rick0x00/8bit-computer/HARDWARE/EDA/DOCUMENTS/ALU.png

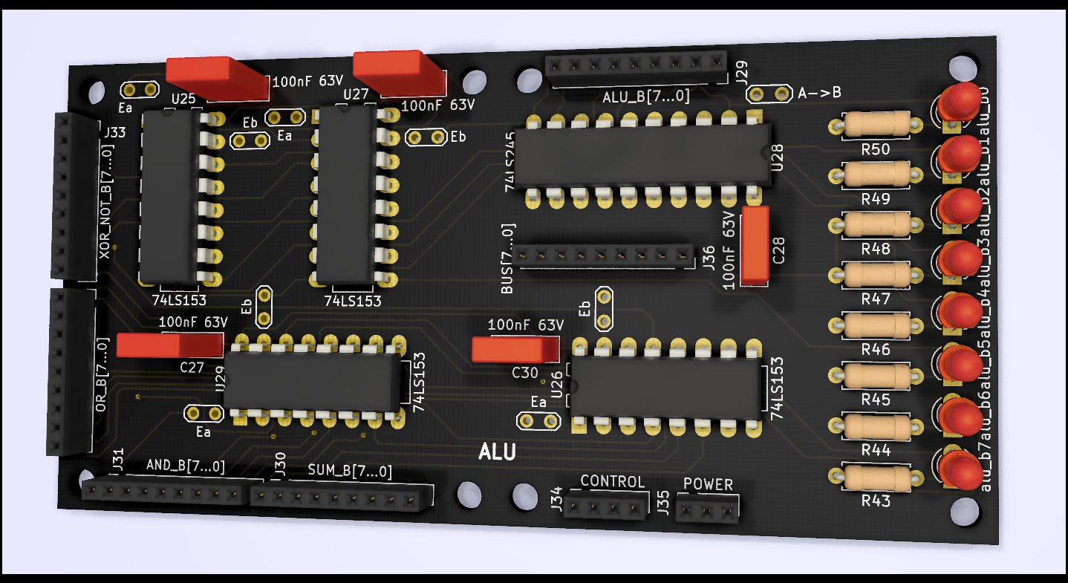
HARDWARE/EDA/DOCUMENTS/ALU.png
