rick0x00/8bit-computer/HARDWARE/EDA/DOCUMENTS/B Register.png

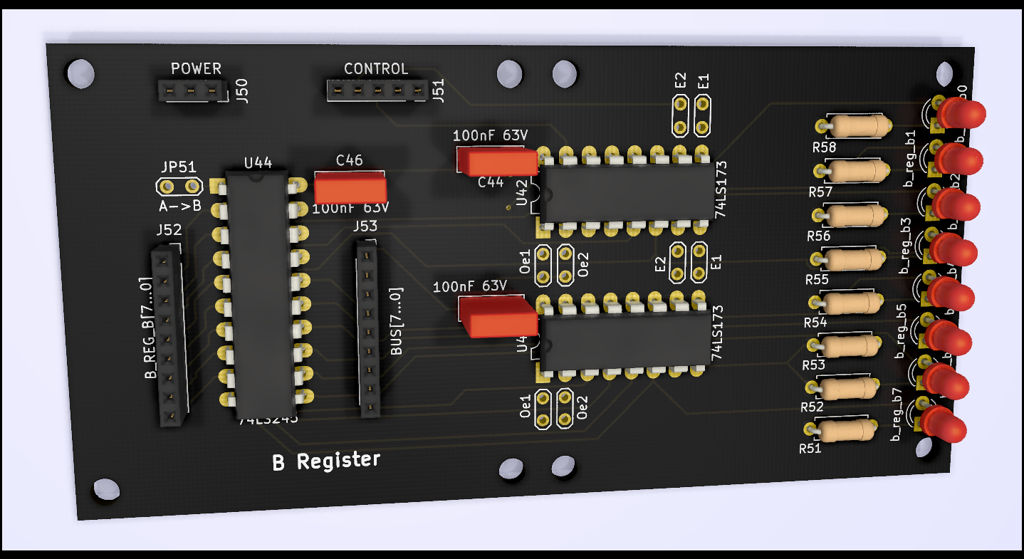
HARDWARE/EDA/DOCUMENTS/B Register.png
