rick0x00/8bit-computer/HARDWARE/EDA/DOCUMENTS/Bus Simulator.png

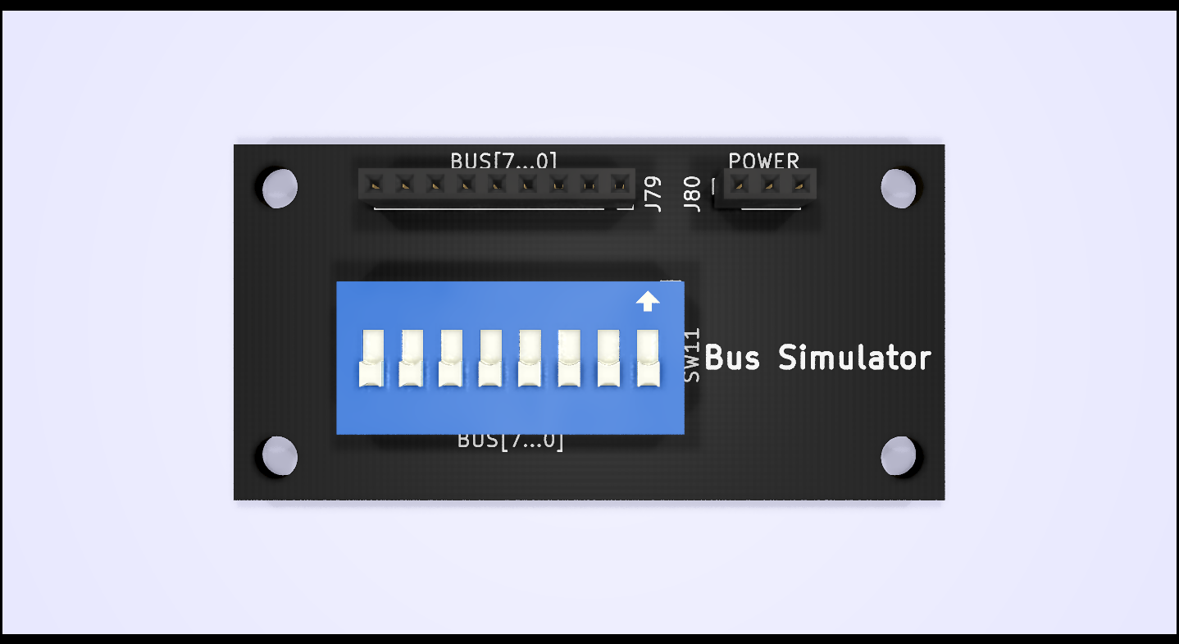
HARDWARE/EDA/DOCUMENTS/Bus Simulator.png
