rick0x00/8bit-computer/HARDWARE/EDA/DOCUMENTS/Clock Circuit.png

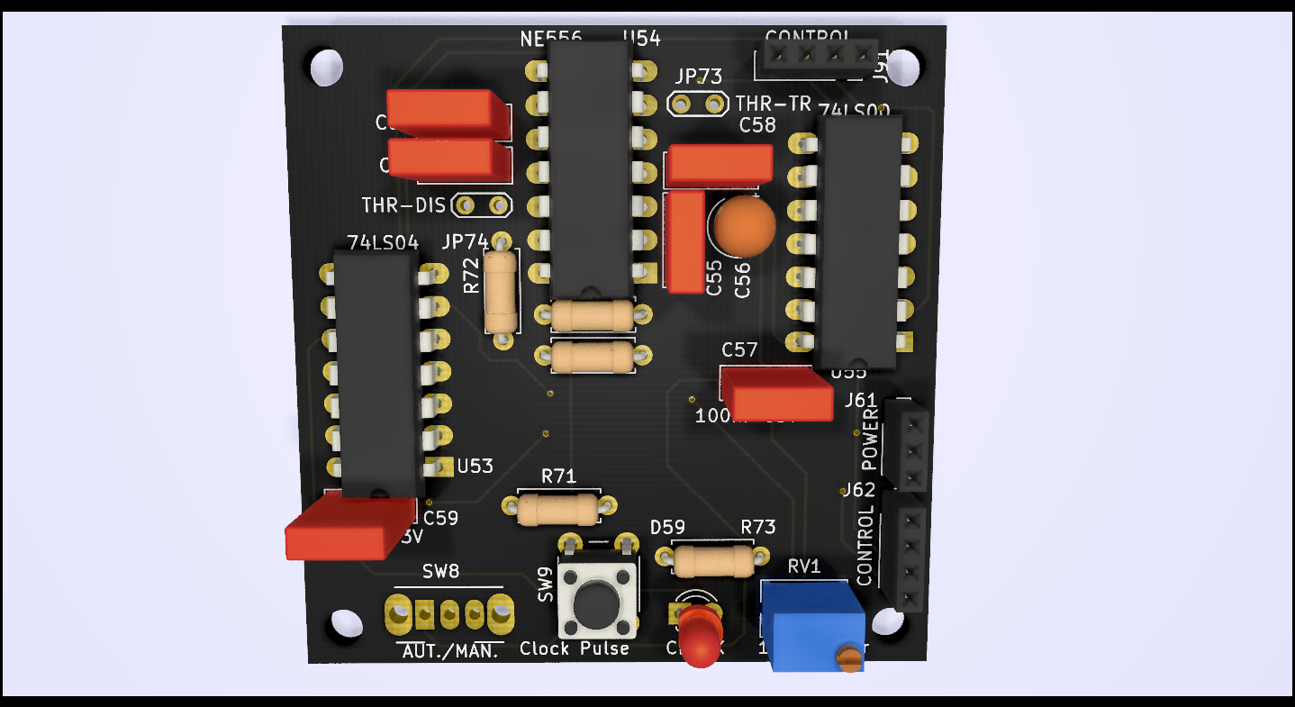
HARDWARE/EDA/DOCUMENTS/Clock Circuit.png
