rick0x00/8bit-computer/HARDWARE/EDA/DOCUMENTS/Control Decoder Simulator.png

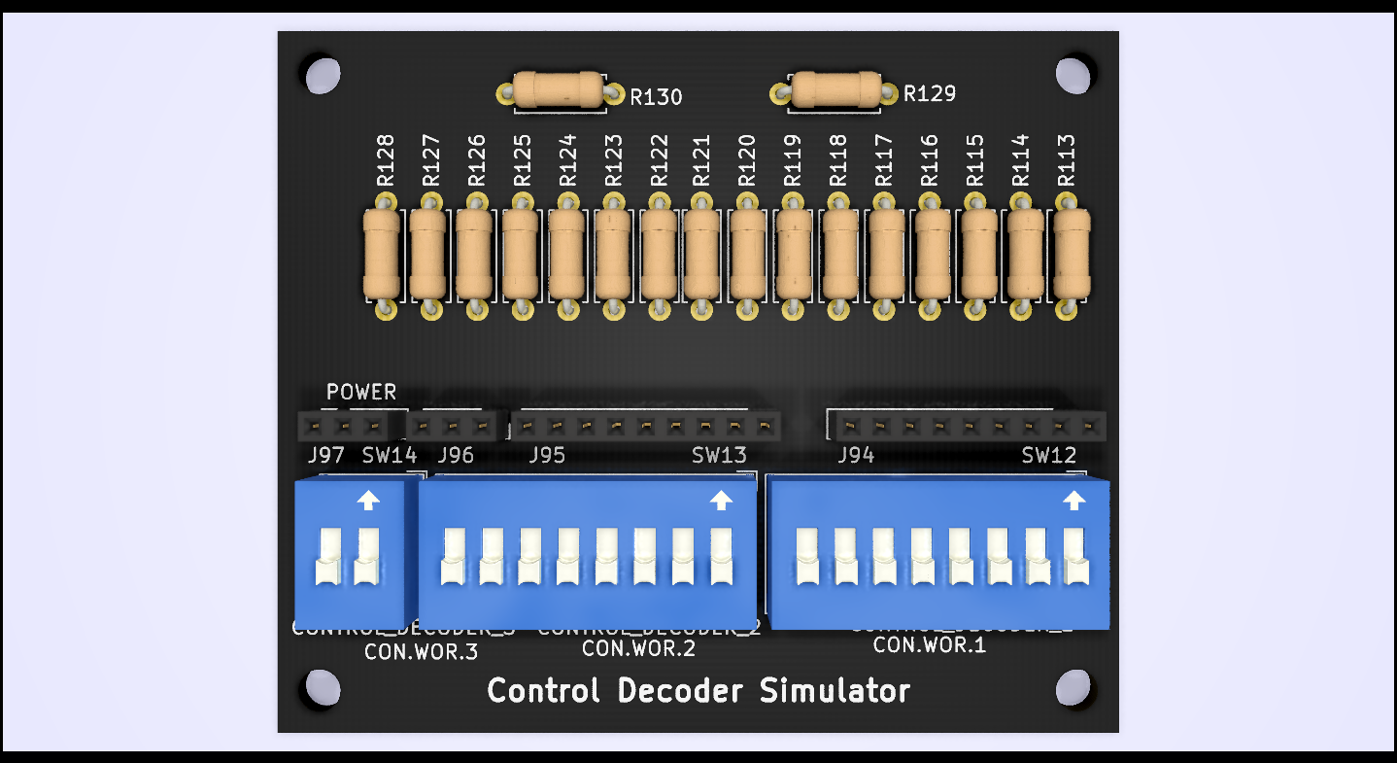
HARDWARE/EDA/DOCUMENTS/Control Decoder Simulator.png
