rick0x00/8bit-computer/HARDWARE/EDA/DOCUMENTS/Control Decoder.png

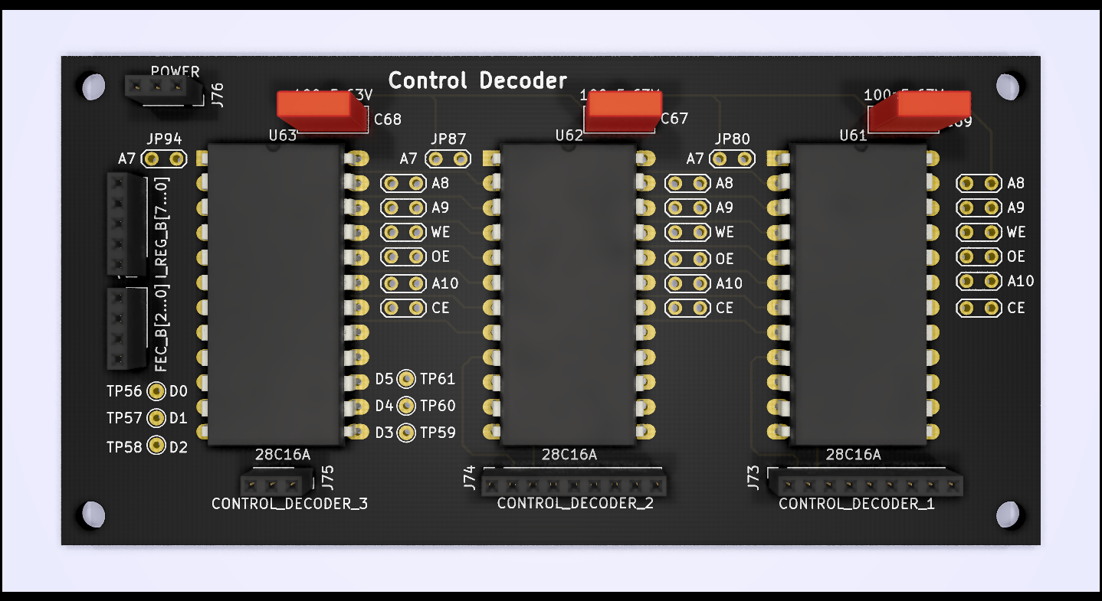
HARDWARE/EDA/DOCUMENTS/Control Decoder.png
