rick0x00/8bit-computer/HARDWARE/EDA/DOCUMENTS/Display.png

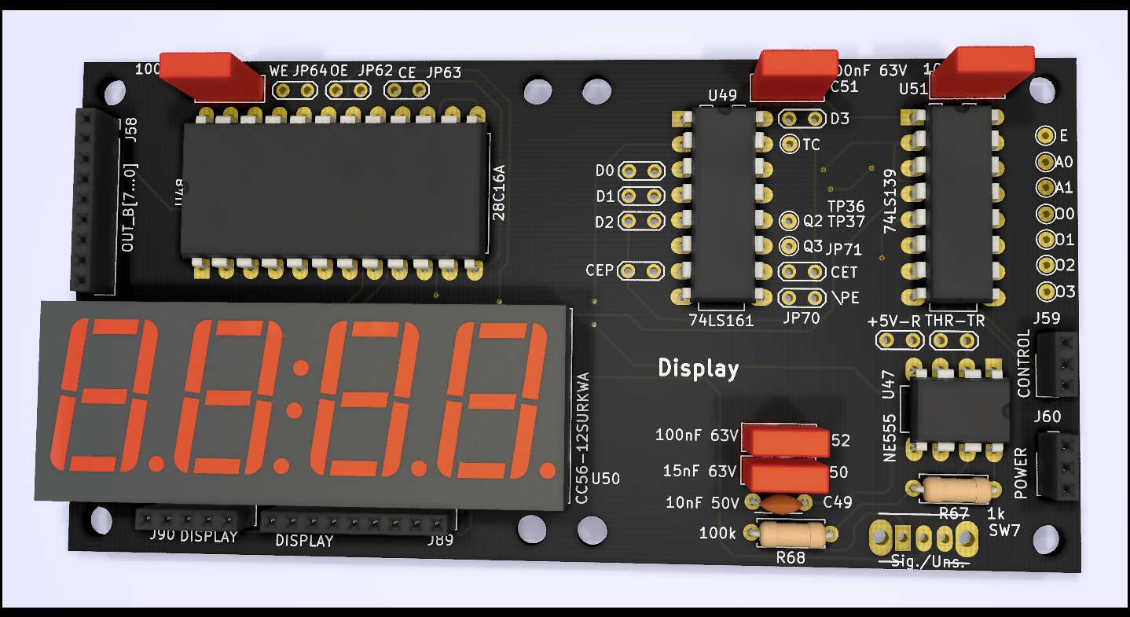
HARDWARE/EDA/DOCUMENTS/Display.png
