rick0x00/8bit-computer/HARDWARE/EDA/DOCUMENTS/hierarchy.png

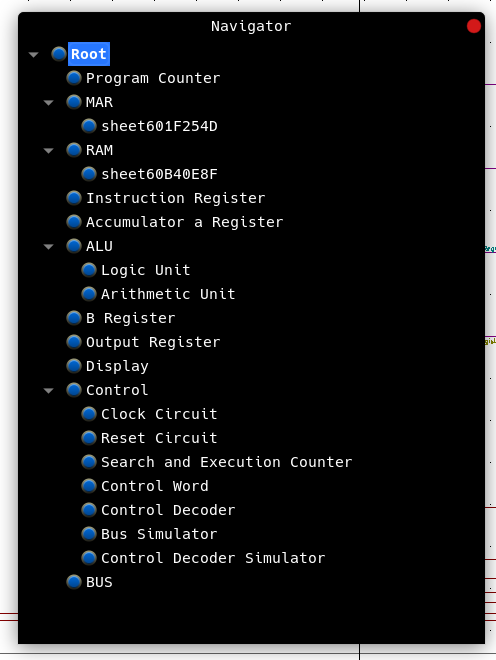
HARDWARE/EDA/DOCUMENTS/hierarchy.png
