rick0x00/8bit-computer/HARDWARE/EDA/DOCUMENTS/Logic Unit.png

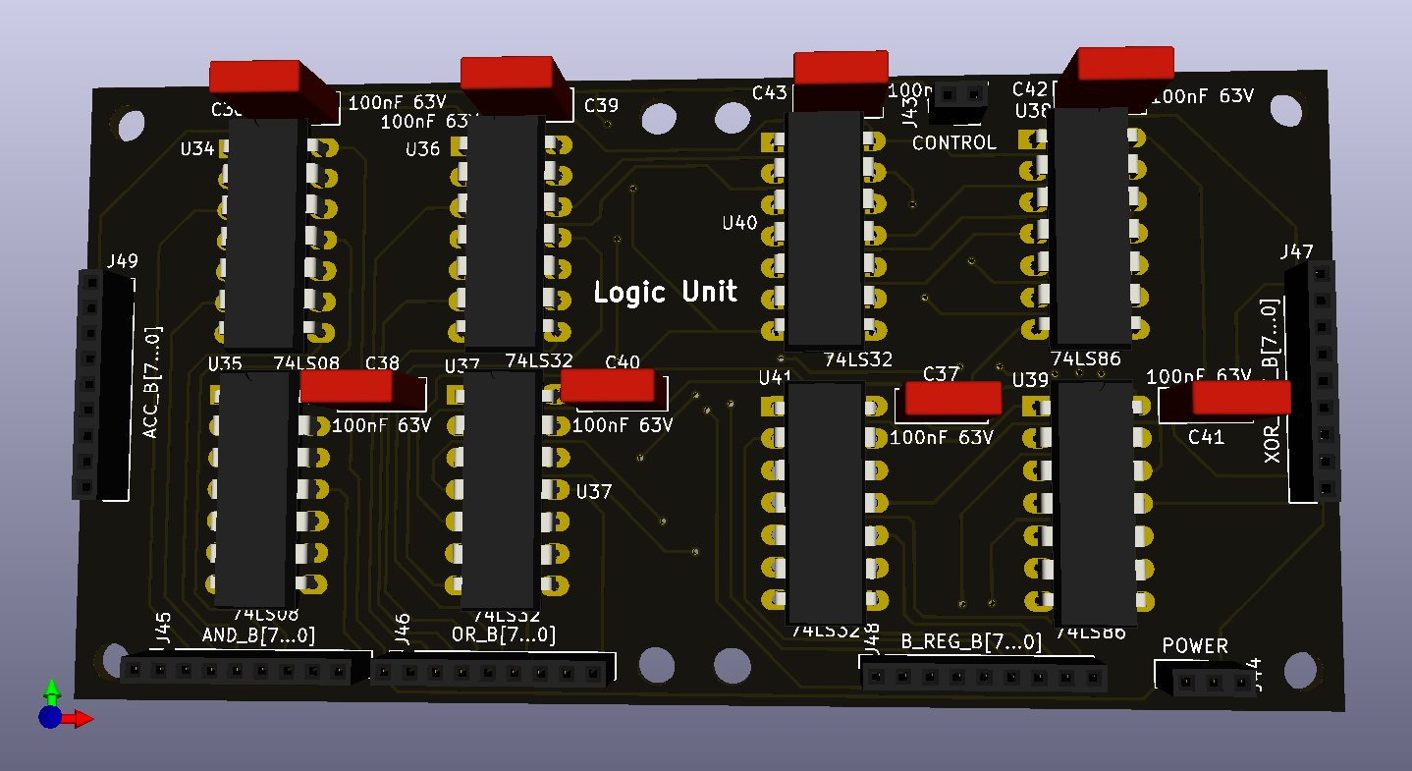
HARDWARE/EDA/DOCUMENTS/Logic Unit.png
