rick0x00/8bit-computer/HARDWARE/EDA/DOCUMENTS/Output Register.png

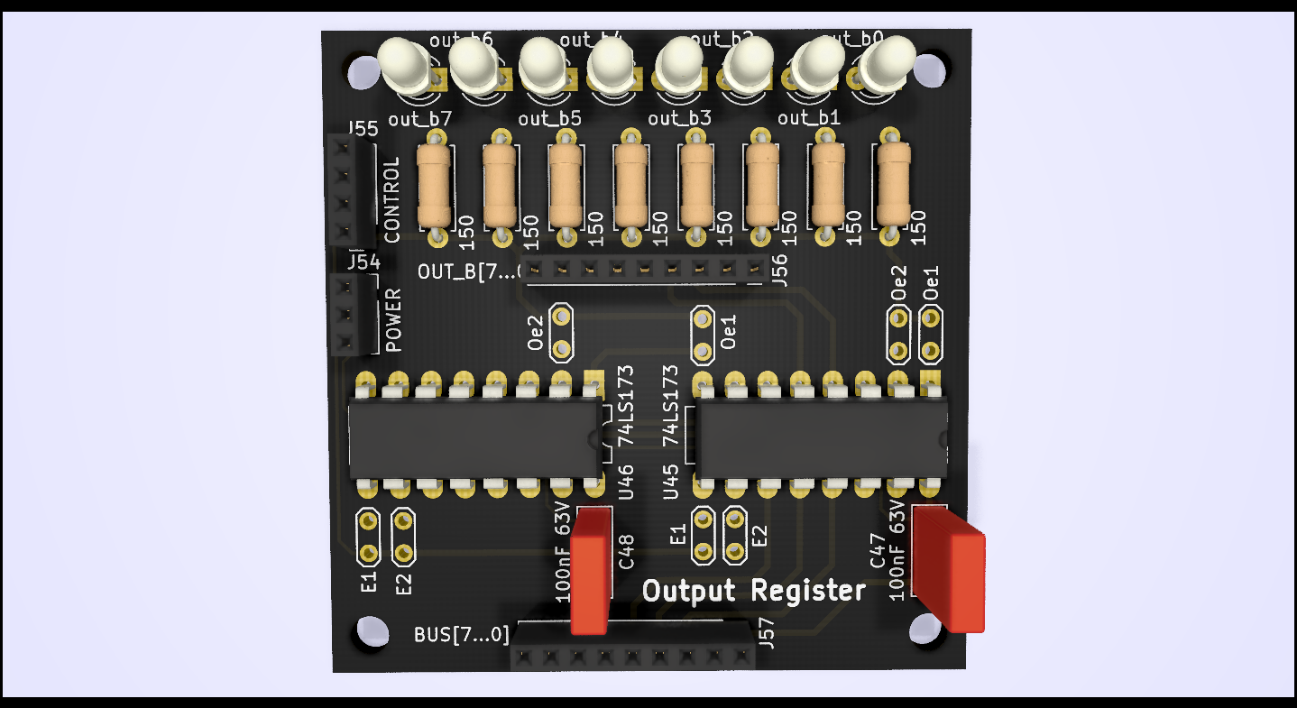
HARDWARE/EDA/DOCUMENTS/Output Register.png
