rick0x00/8bit-computer/HARDWARE/EDA/DOCUMENTS/Program Counter.png

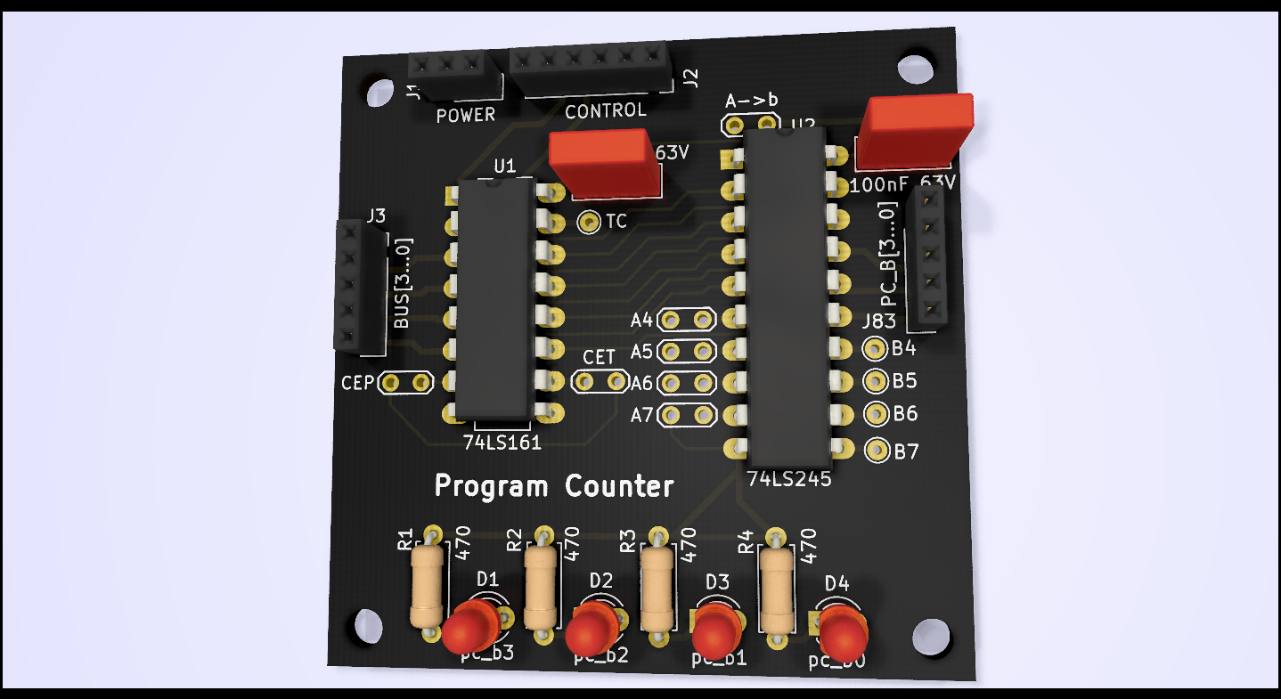
HARDWARE/EDA/DOCUMENTS/Program Counter.png
