rick0x00/8bit-computer/HARDWARE/EDA/DOCUMENTS/RAM.png

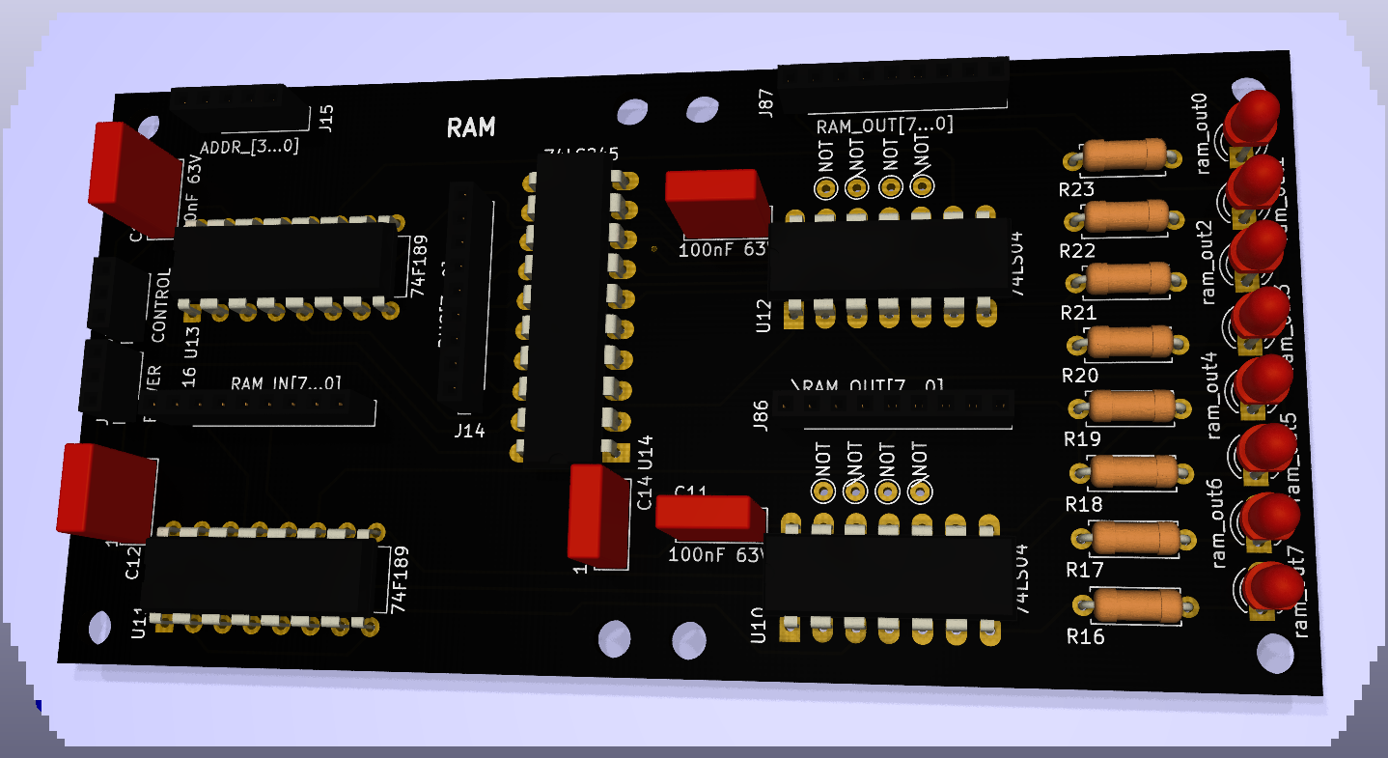
HARDWARE/EDA/DOCUMENTS/RAM.png
