rick0x00/8bit-computer/HARDWARE/EDA/DOCUMENTS/Search and Execution Counter.png

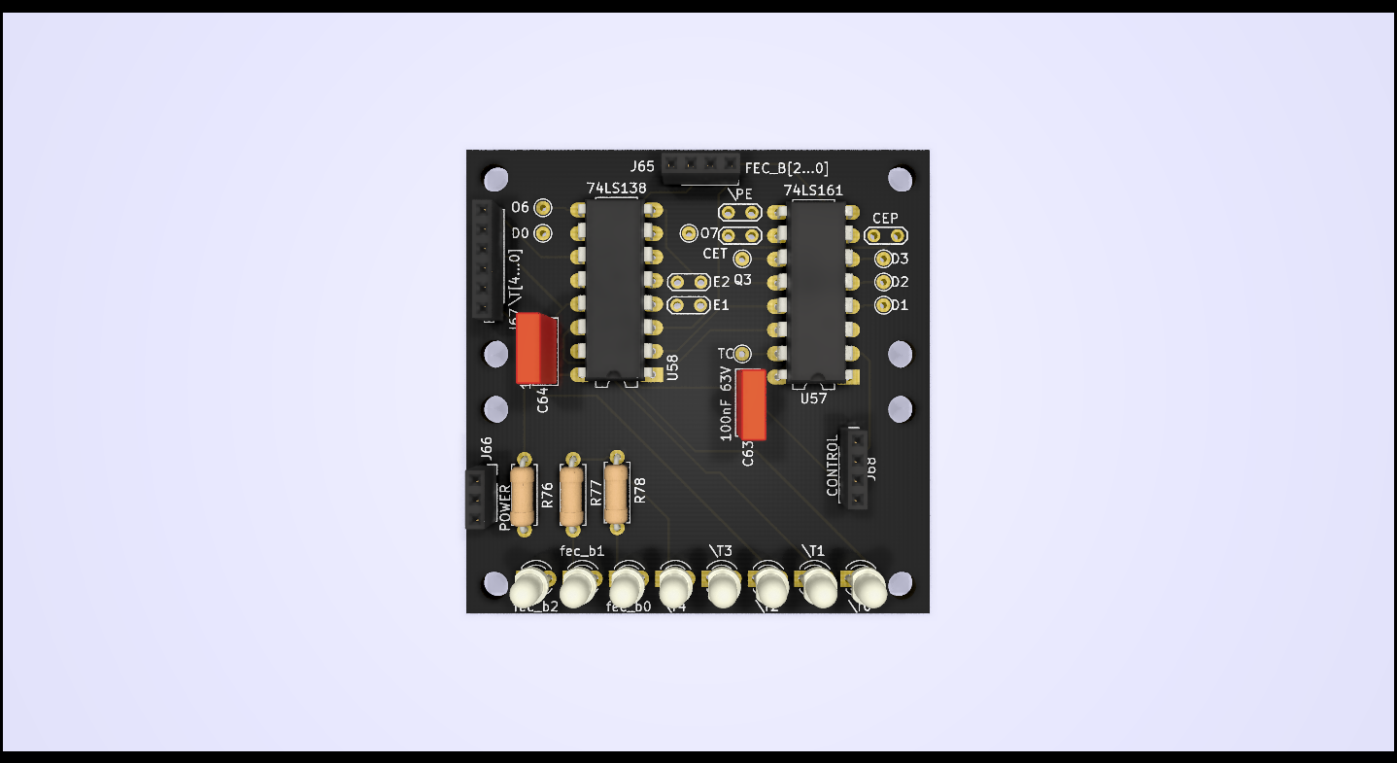
HARDWARE/EDA/DOCUMENTS/Search and Execution Counter.png
