rick0x00/8bit-computer/HARDWARE/EDA/DOCUMENTS/Selection Circuit.png

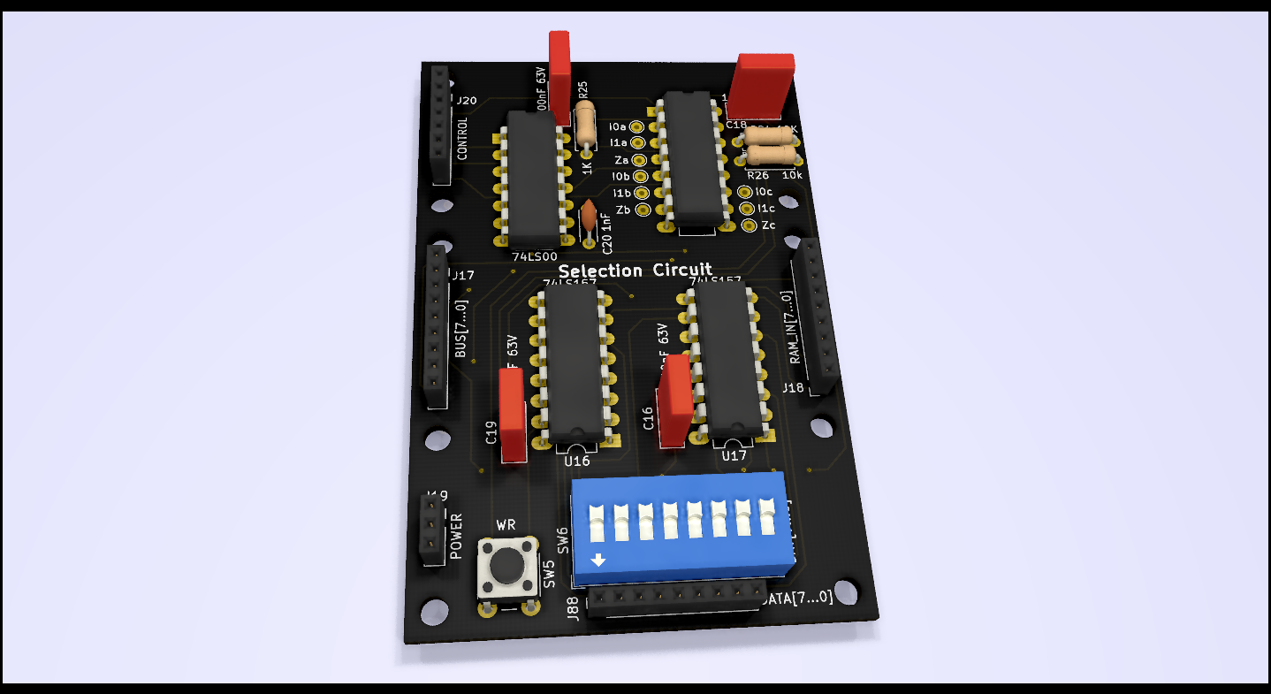
HARDWARE/EDA/DOCUMENTS/Selection Circuit.png
