rick0x00/8bit-computer/HARDWARE/EDA/DOCUMENTS/Instruction Register.png

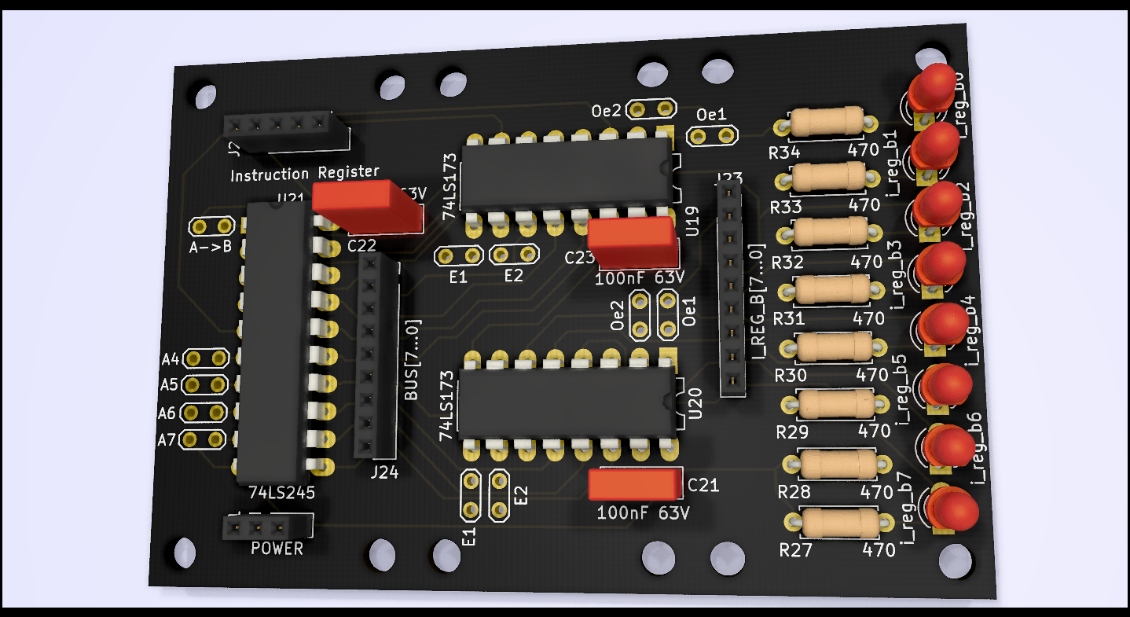
HARDWARE/EDA/DOCUMENTS/Instruction Register.png
