rick0x00/8bit-computer/HARDWARE/EDA/DOCUMENTS/BUS PCB.pdf

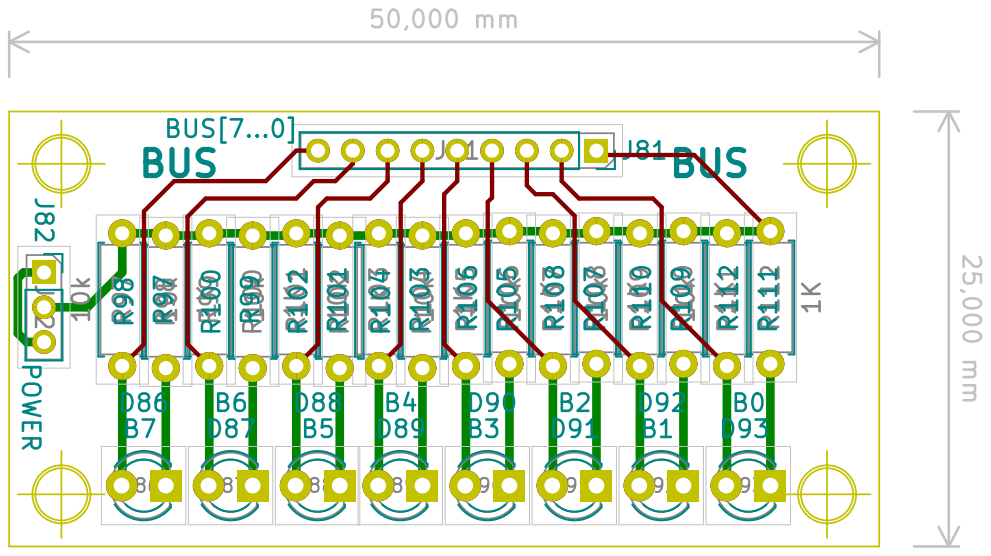
[picture p35: page 1]
