rick0x00/8bit-computer/HARDWARE/EDA/DOCUMENTS/Bus Simulator Black PCB.pdf

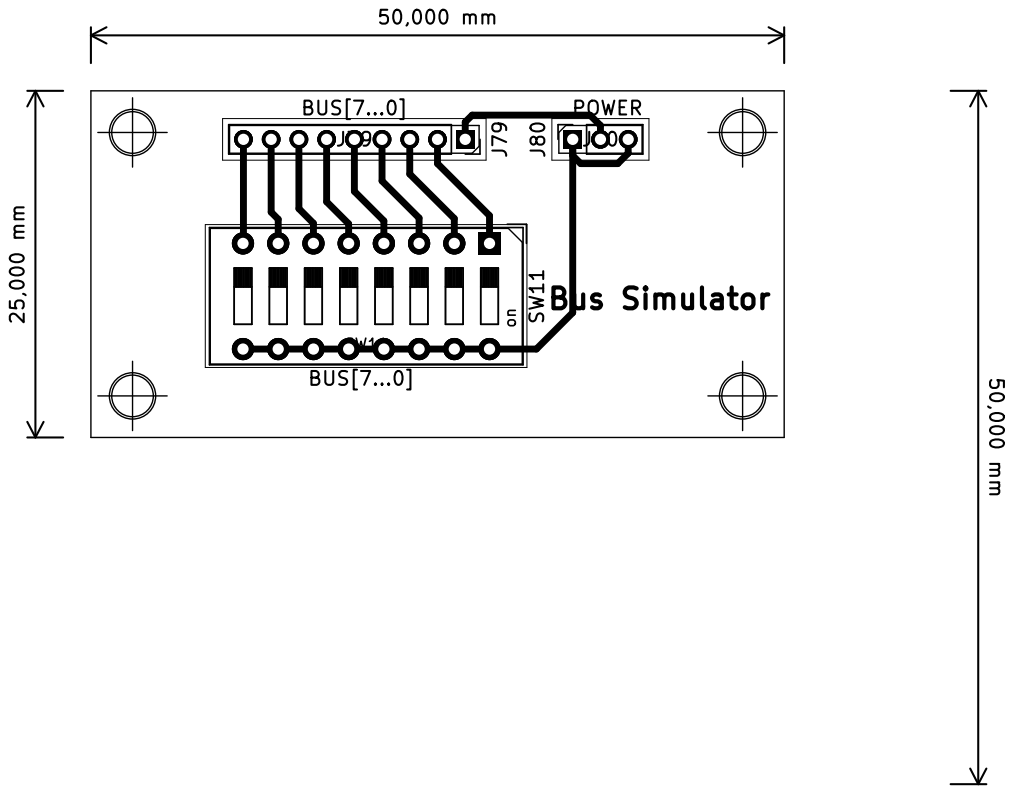
[picture p36: page 1]
