rick0x00/8bit-computer/HARDWARE/EDA/DOCUMENTS/Bus Simulator PCB.pdf

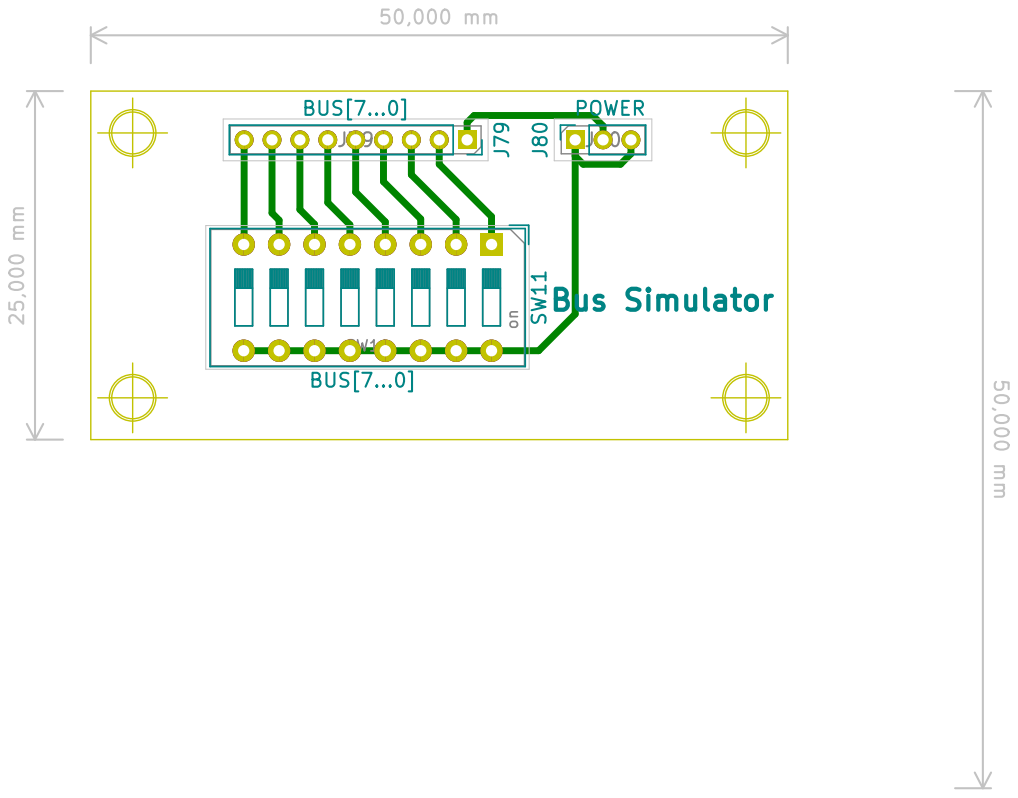
[picture p37: page 1]
