rick0x00/8bit-computer/HARDWARE/EDA/DOCUMENTS/Clock Circuit Black PCB.pdf

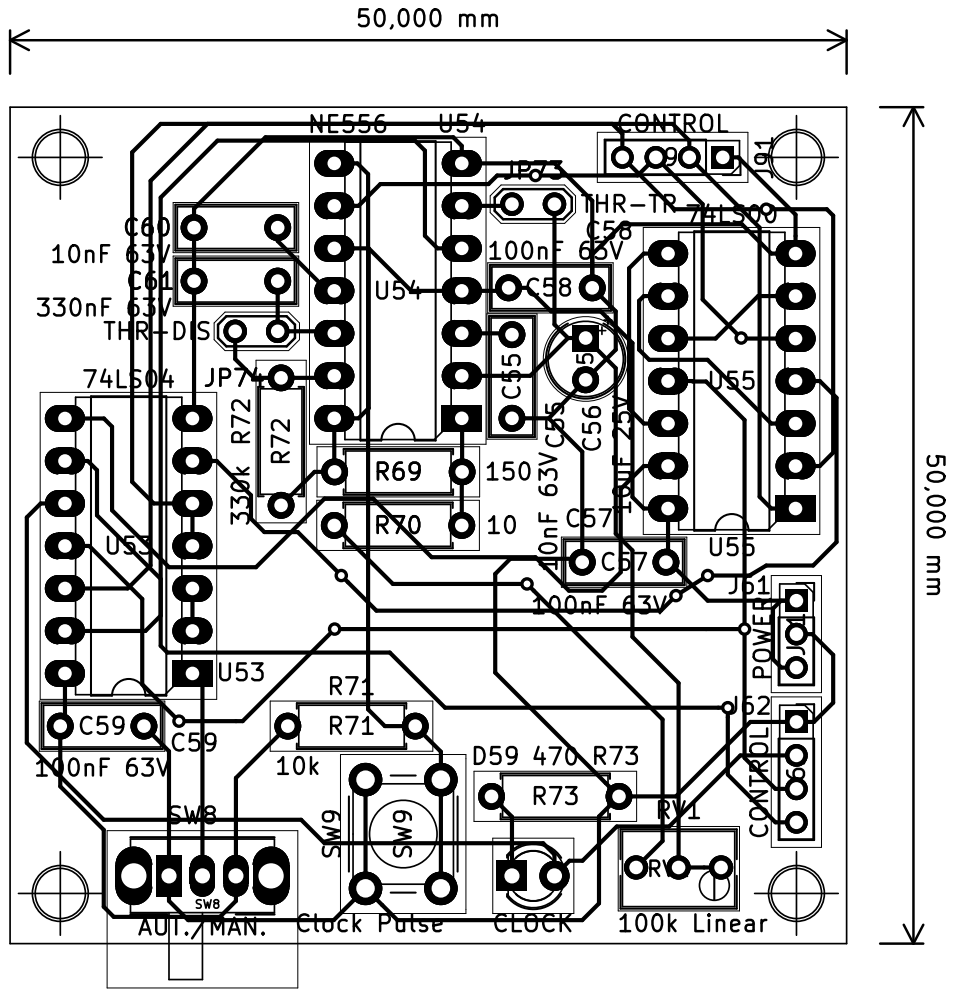
[picture p38: page 1]
