rick0x00/8bit-computer/HARDWARE/EDA/DOCUMENTS/Clock Circuit PCB.pdf

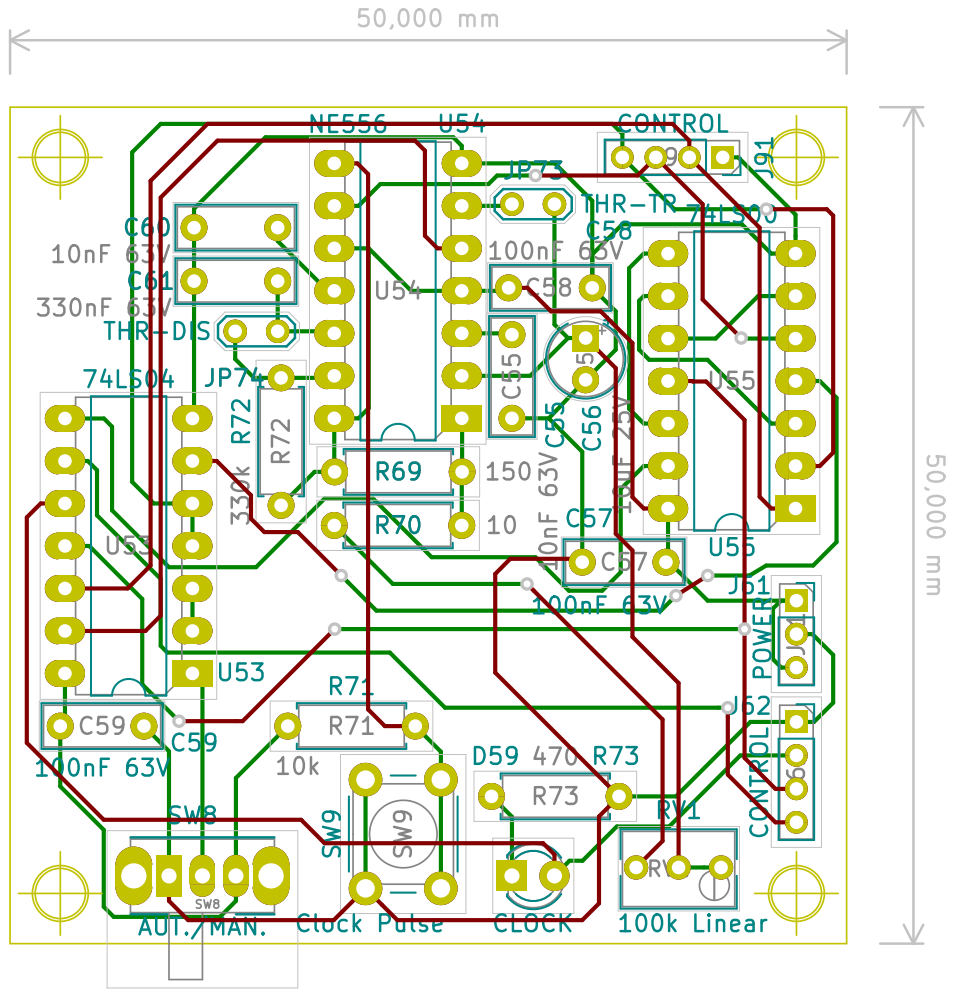
[picture p39: page 1]
