rick0x00/8bit-computer/HARDWARE/EDA/DOCUMENTS/Control Decoder Black PCB.pdf

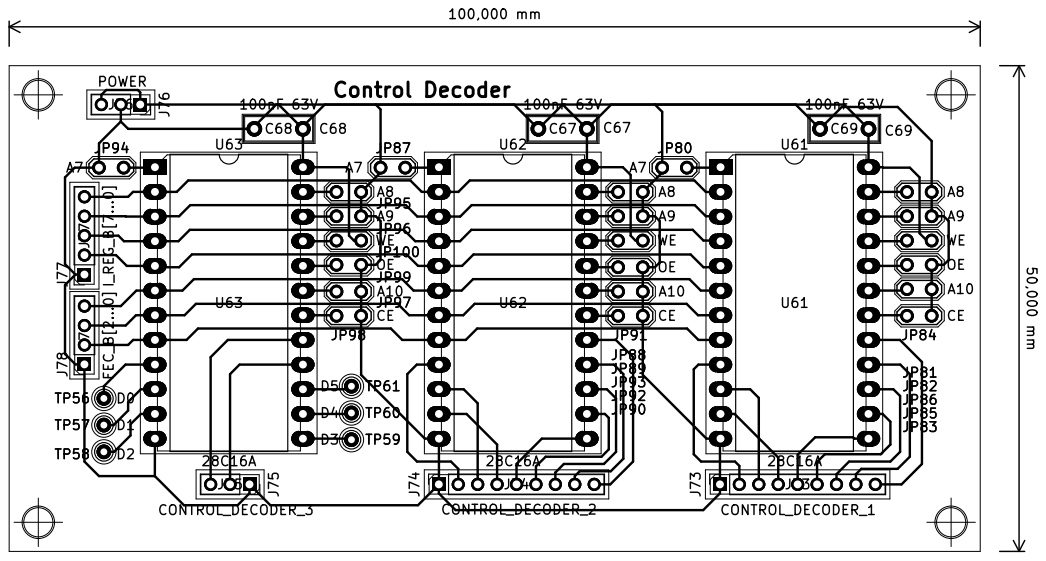
[picture p40: page 1]
