rick0x00/8bit-computer/HARDWARE/EDA/DOCUMENTS/Control Decoder PCB.pdf

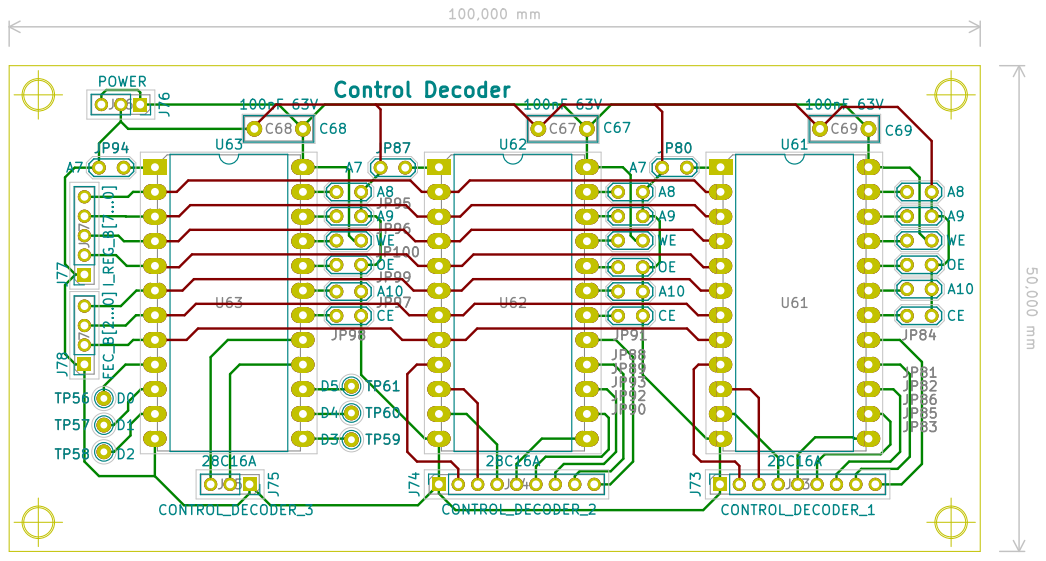
[picture p41: page 1]
