rick0x00/8bit-computer/HARDWARE/EDA/DOCUMENTS/Control Decoder Simulator Black PCB.pdf

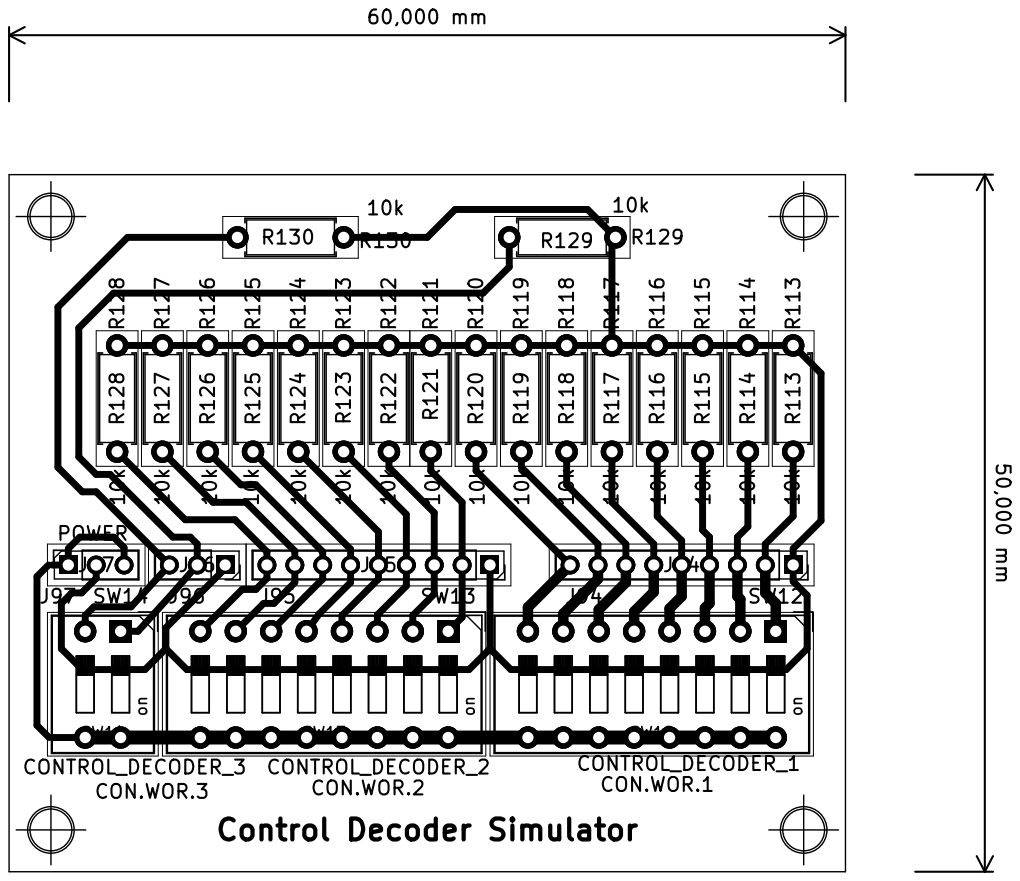
[picture p42: page 1]
