rick0x00/8bit-computer/HARDWARE/EDA/DOCUMENTS/Control Decoder Simulator PCB.pdf

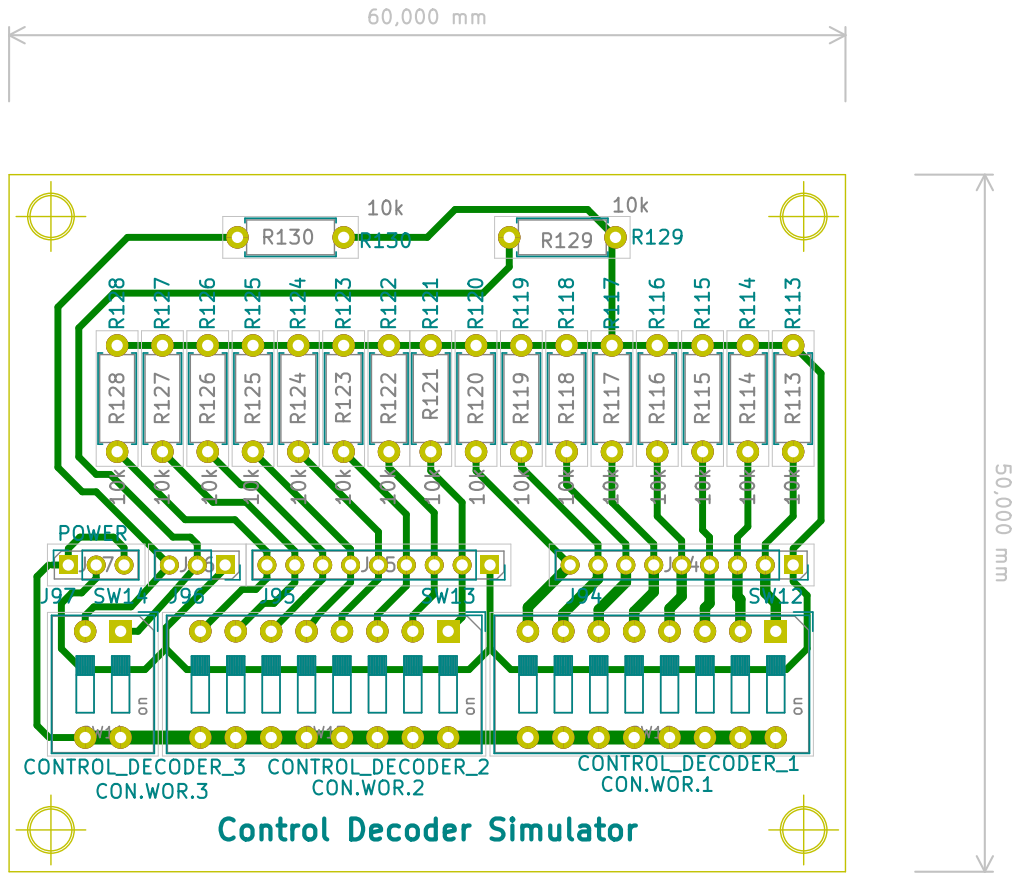
[picture p43: page 1]
