rick0x00/8bit-computer/HARDWARE/EDA/DOCUMENTS/Control Word Black PCB.pdf

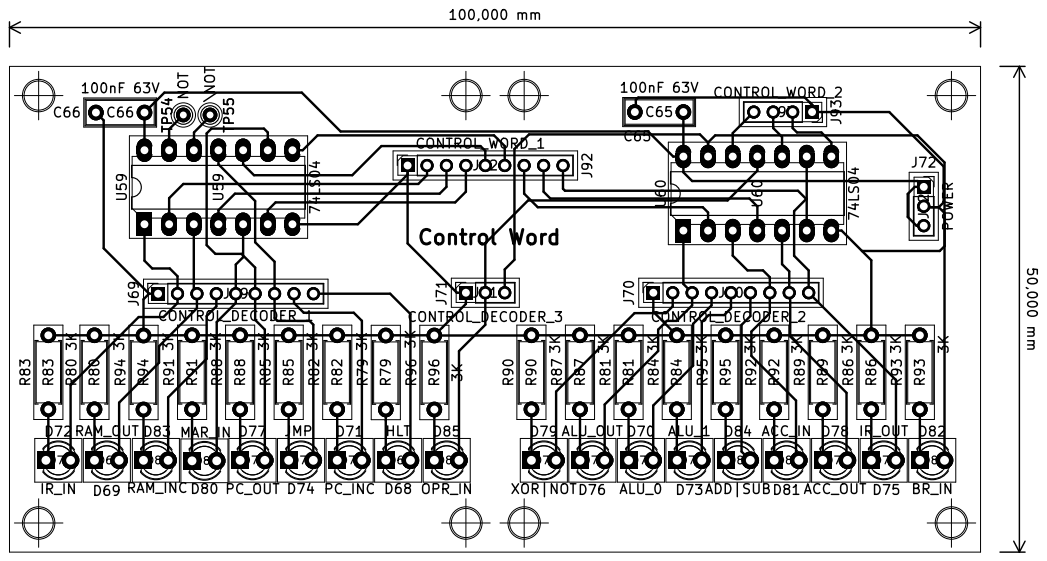
[picture p44: page 1]
