rick0x00/8bit-computer/HARDWARE/EDA/DOCUMENTS/Control Word PCB.pdf

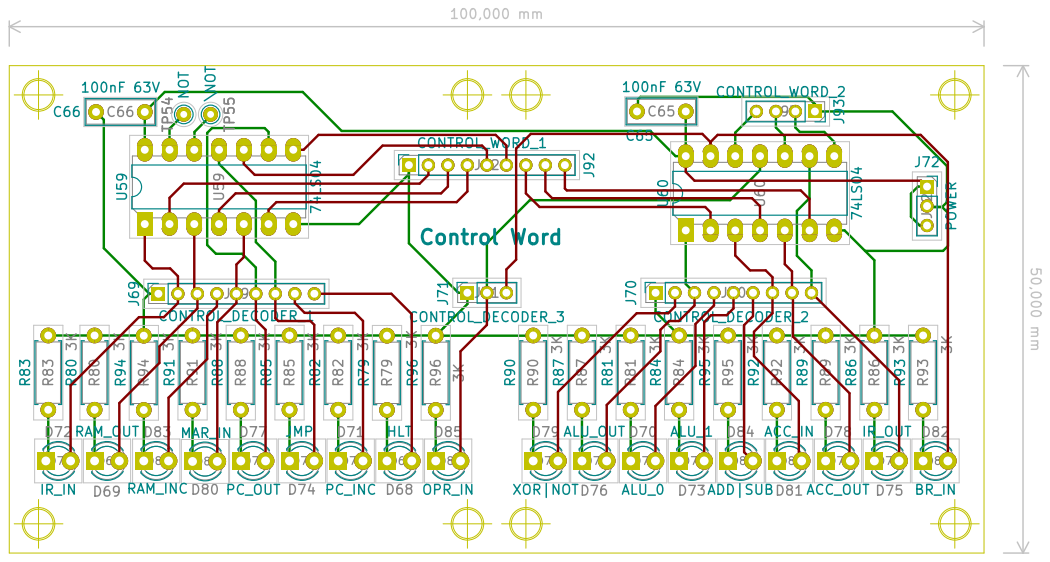
[picture p45: page 1]
