rick0x00/8bit-computer/HARDWARE/EDA/DOCUMENTS/Display Black PCB.pdf

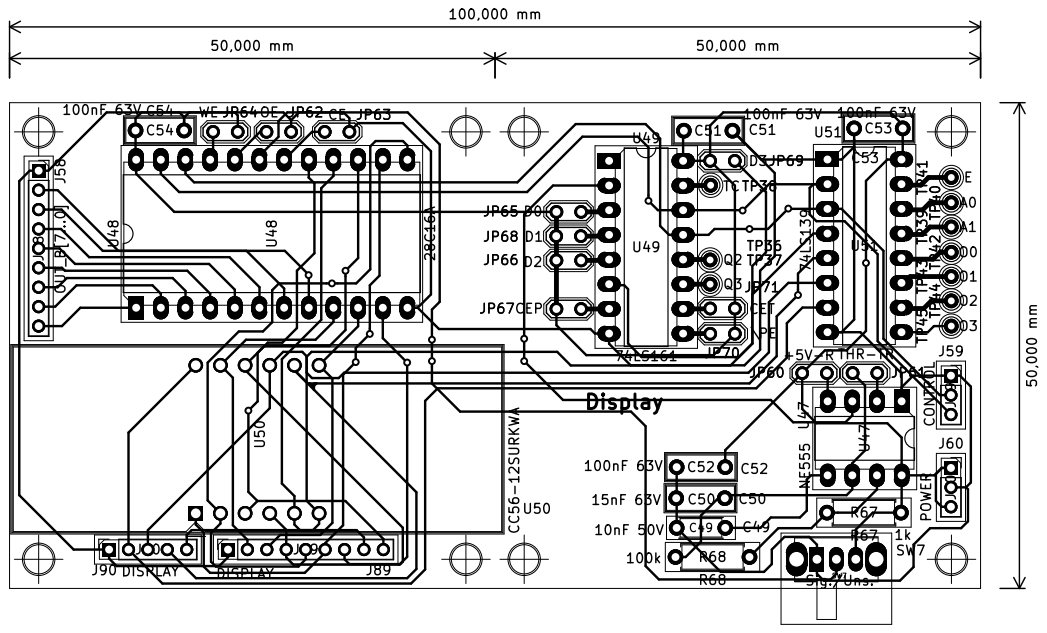
[picture p46: page 1]
