rick0x00/8bit-computer/HARDWARE/EDA/DOCUMENTS/Display PCB.pdf

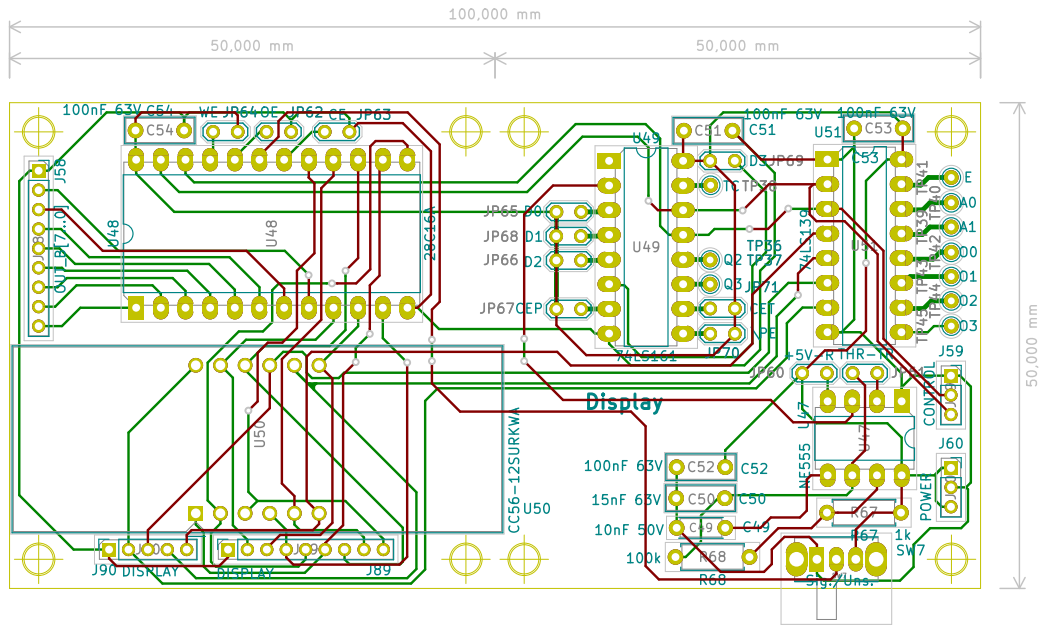
[picture p47: page 1]
