rick0x00/8bit-computer/HARDWARE/EDA/DOCUMENTS/Instruction Register Black PCB.pdf

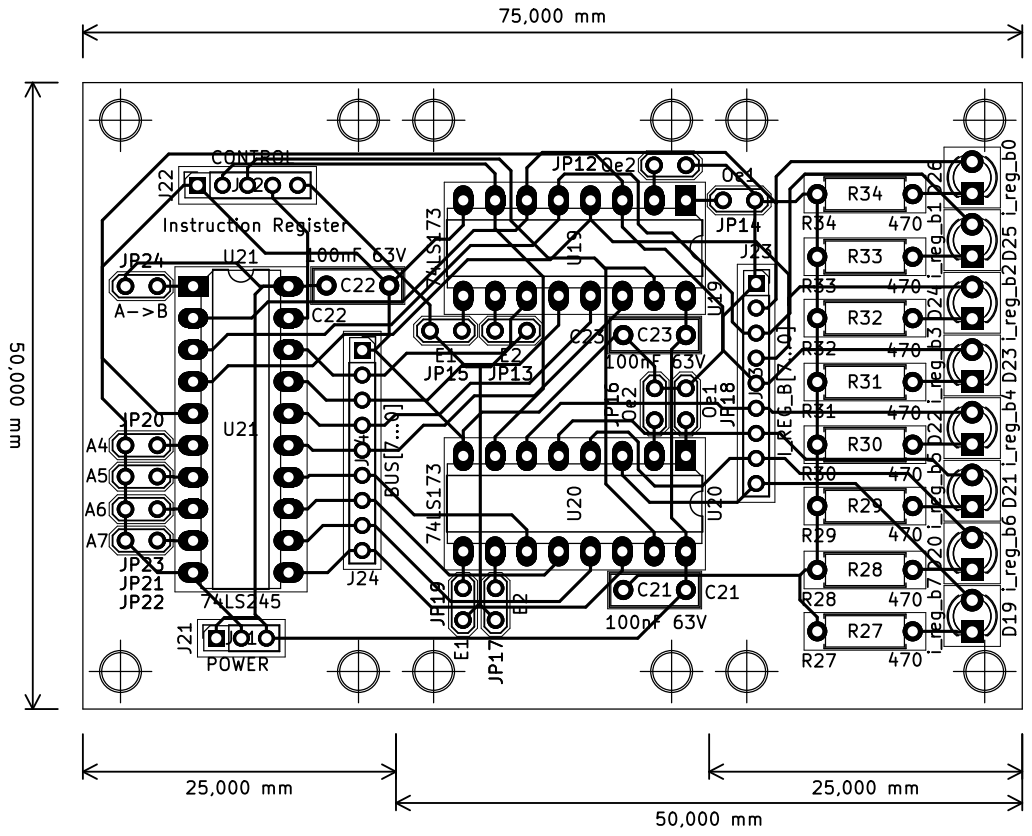
[picture p48: page 1]
