rick0x00/8bit-computer/HARDWARE/EDA/DOCUMENTS/Instruction Register PCB.pdf

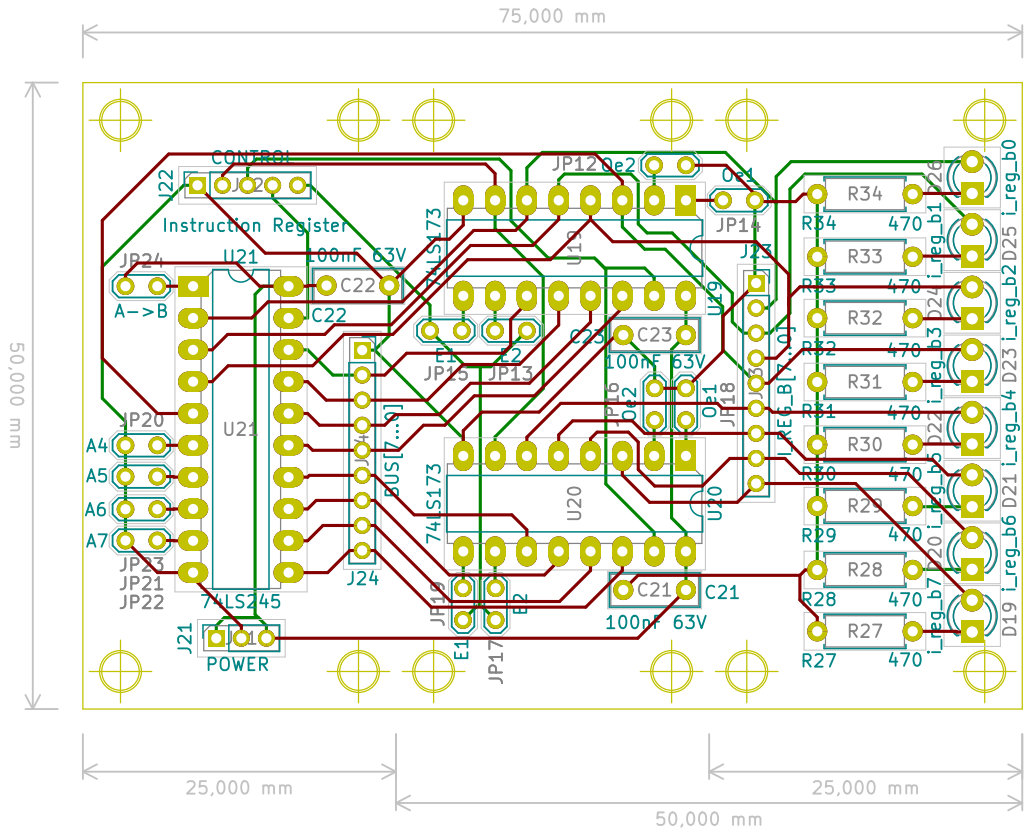
[picture p49: page 1]
