rick0x00/8bit-computer/HARDWARE/EDA/DOCUMENTS/Logic Unit Black PCB.pdf

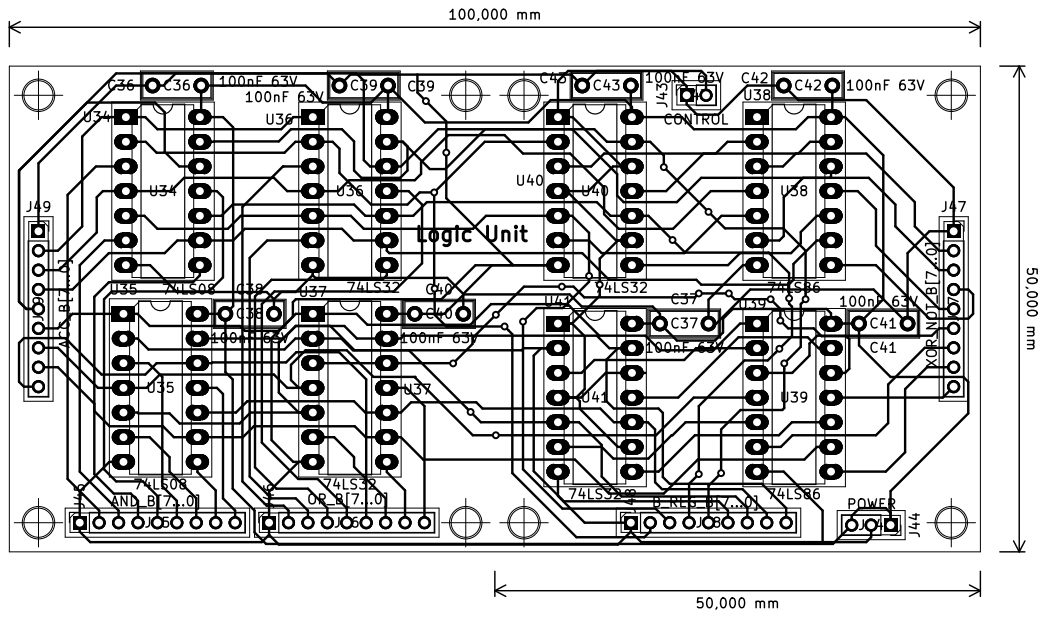
[picture p50: page 1]
