rick0x00/8bit-computer/HARDWARE/EDA/DOCUMENTS/Logic Unit PCB.pdf

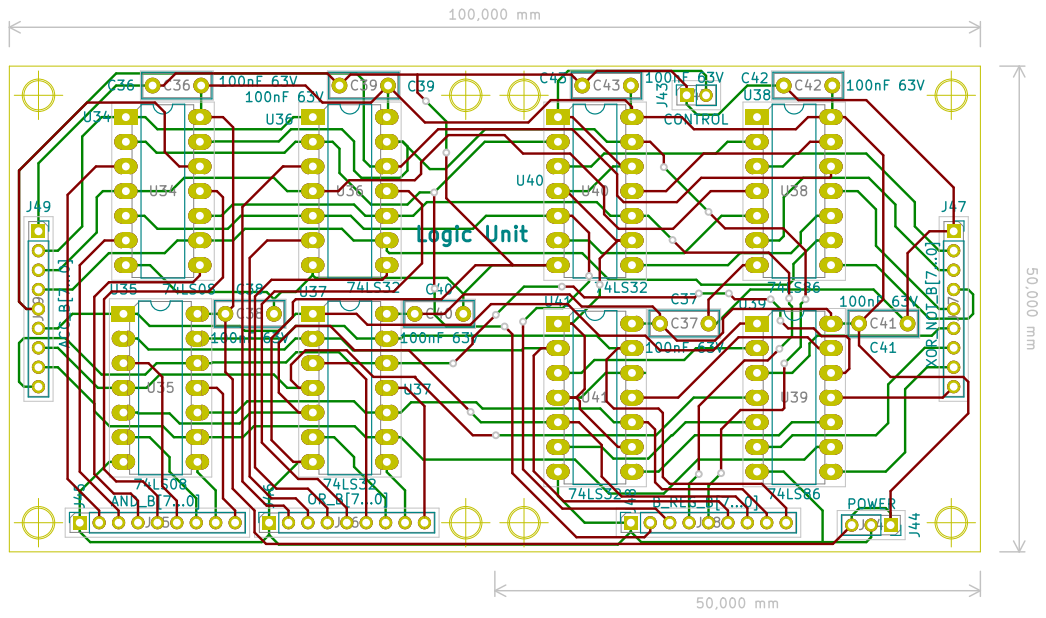
[picture p51: page 1]
