rick0x00/8bit-computer/HARDWARE/EDA/DOCUMENTS/MAR Black PCB.pdf

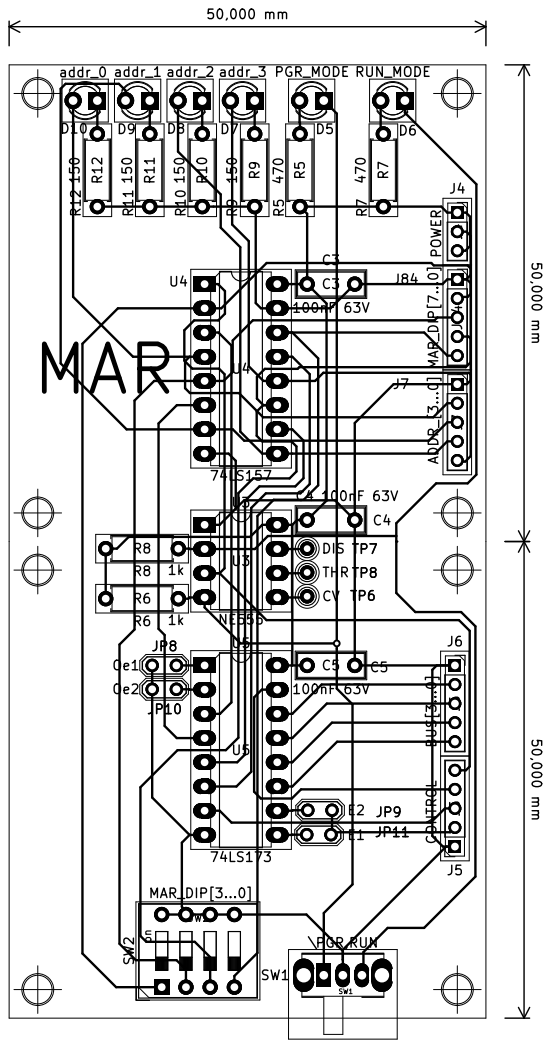
[picture p52: page 1]
