rick0x00/8bit-computer/HARDWARE/EDA/DOCUMENTS/MAR PCB.pdf

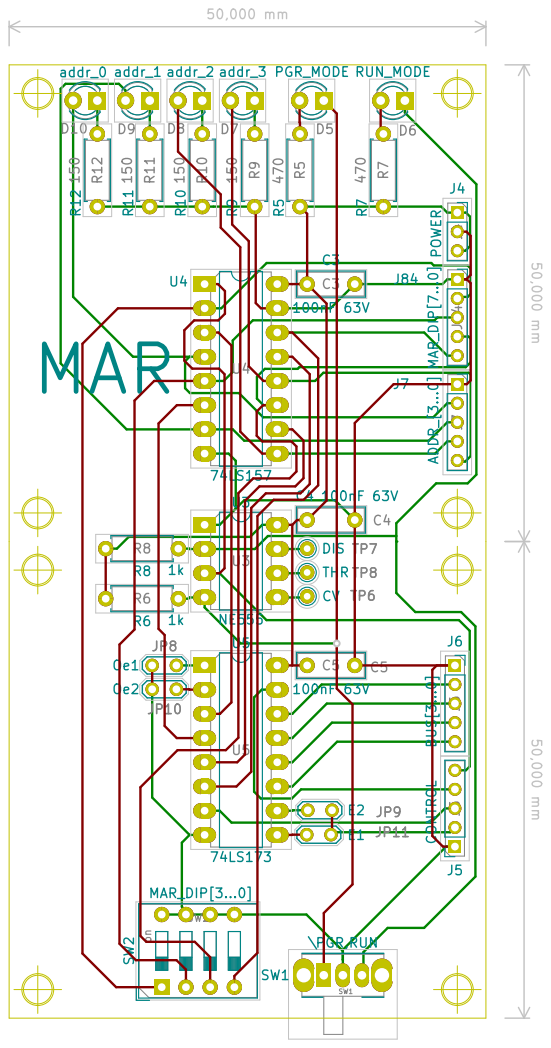
[picture p53: page 1]
