rick0x00/8bit-computer/HARDWARE/EDA/DOCUMENTS/Output Register Black PCB.pdf

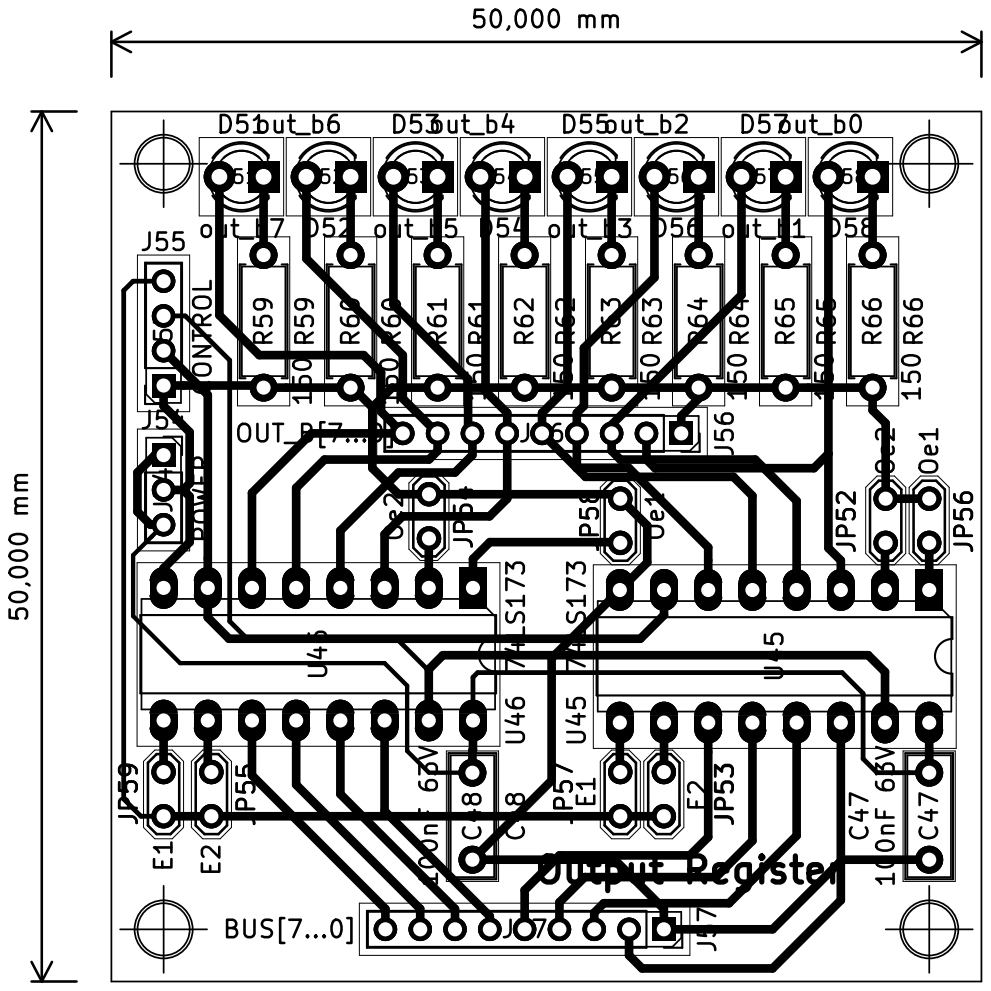
[picture p54: page 1]
