rick0x00/8bit-computer/HARDWARE/EDA/DOCUMENTS/Output Register PCB.pdf

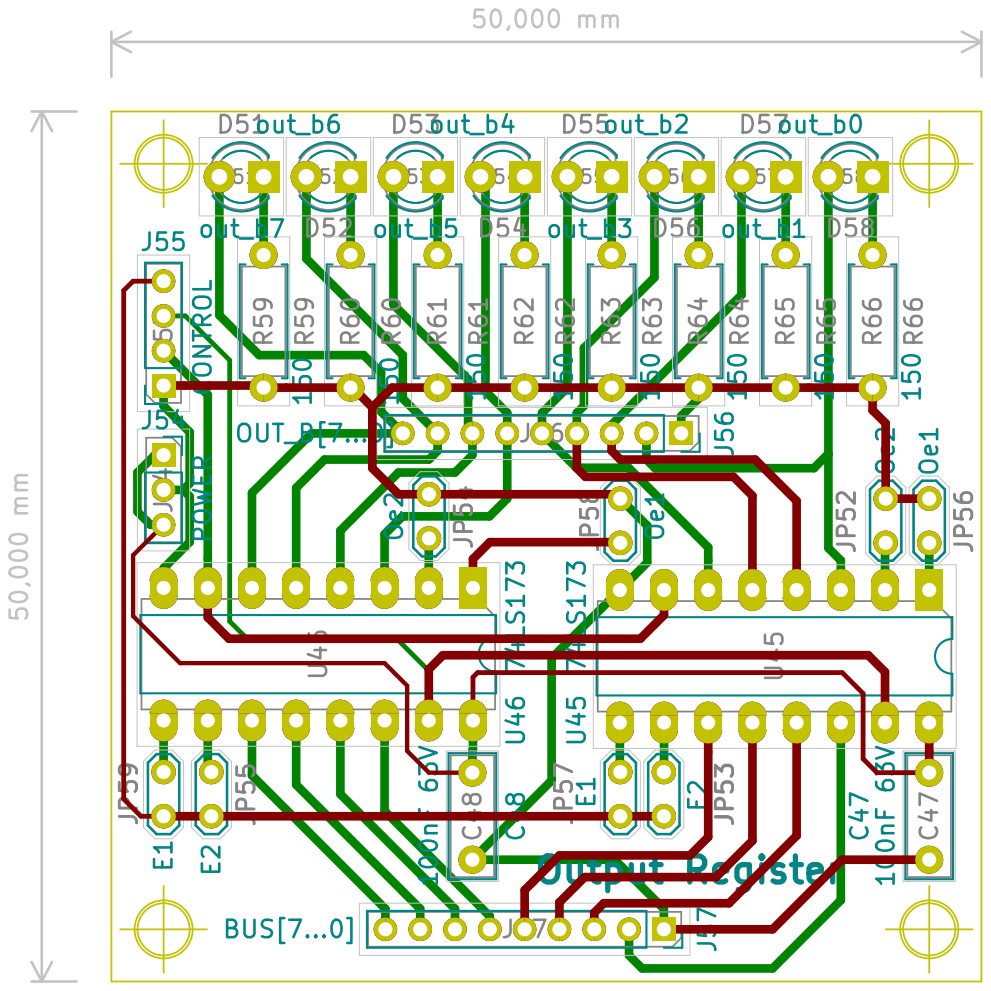
[picture p55: page 1]
