rick0x00/8bit-computer/HARDWARE/EDA/DOCUMENTS/Progra Counter Black PCB.pdf

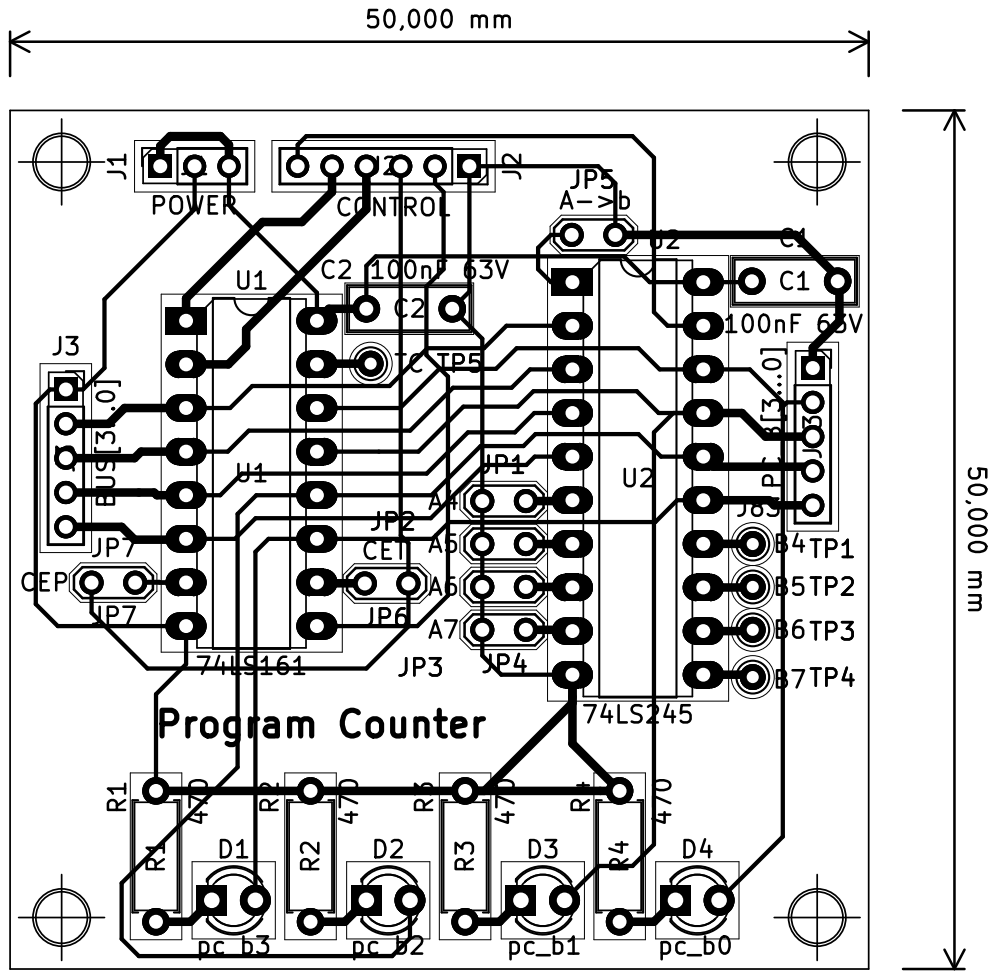
[picture p56: page 1]
