rick0x00/8bit-computer/HARDWARE/EDA/DOCUMENTS/Progra Counter PCB.pdf

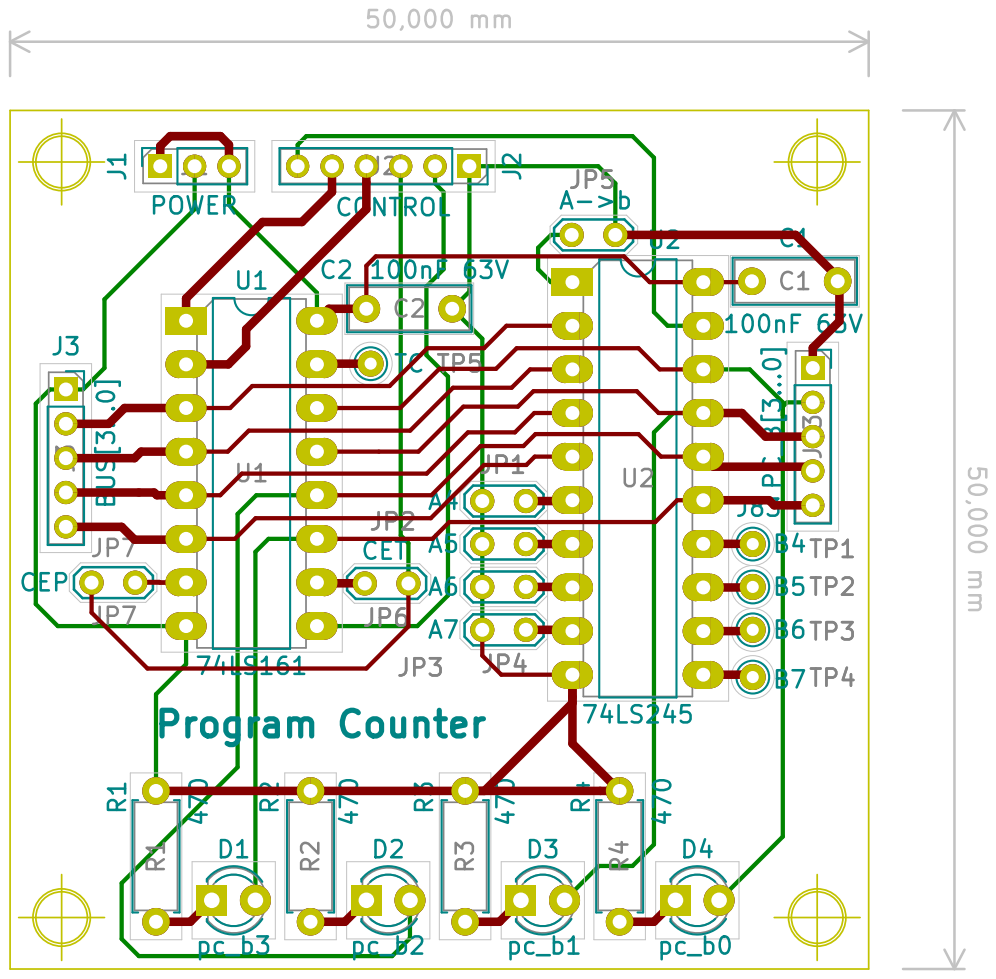
[picture p57: page 1]
