rick0x00/8bit-computer/HARDWARE/EDA/DOCUMENTS/RAM Black PCB.pdf

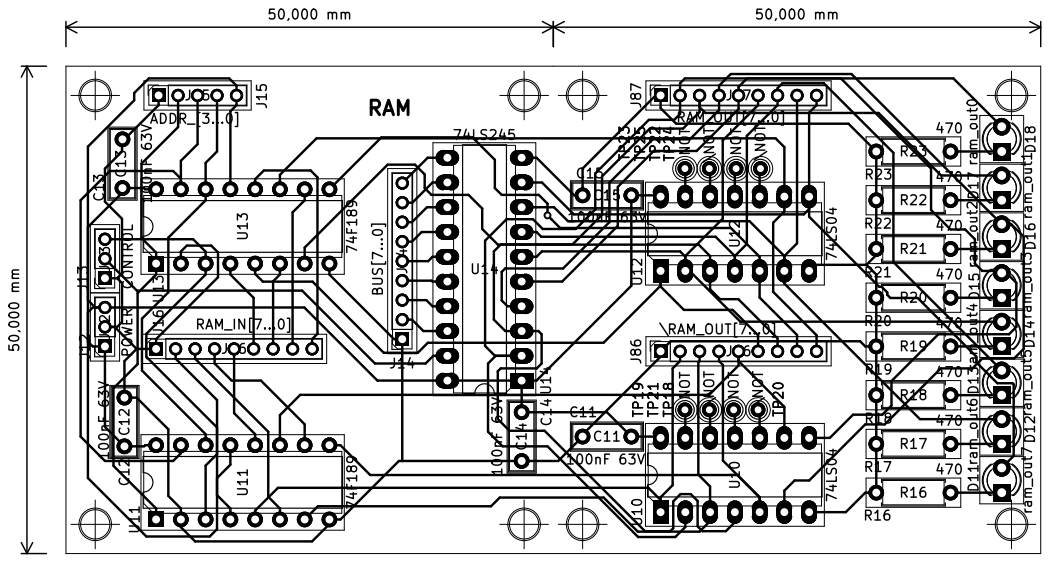
[picture p58: page 1]
