rick0x00/8bit-computer/HARDWARE/EDA/DOCUMENTS/RAM PCB.pdf

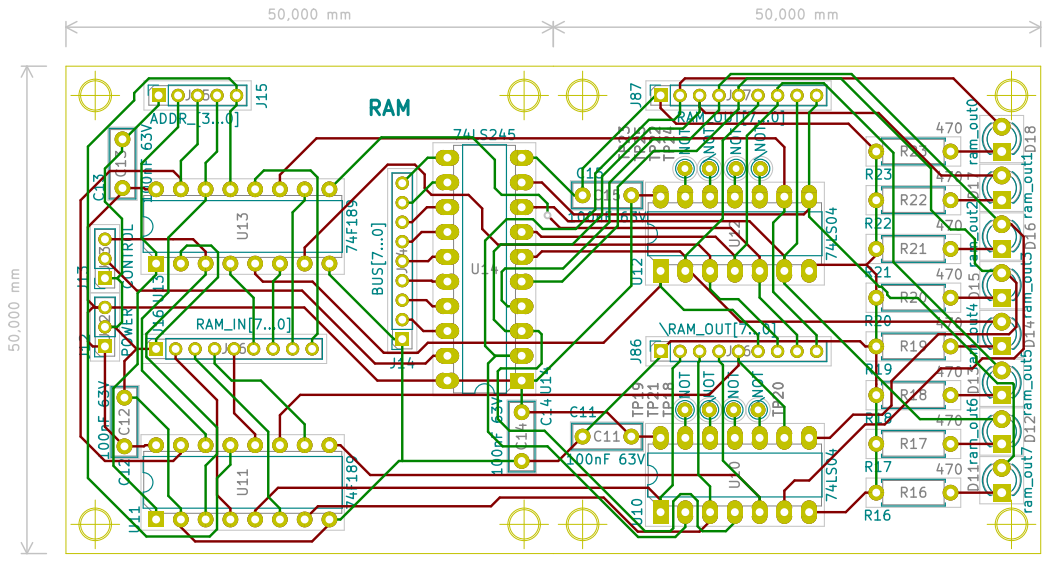
[picture p59: page 1]
