rick0x00/8bit-computer/HARDWARE/EDA/DOCUMENTS/Reset Circuit Black PCB.pdf

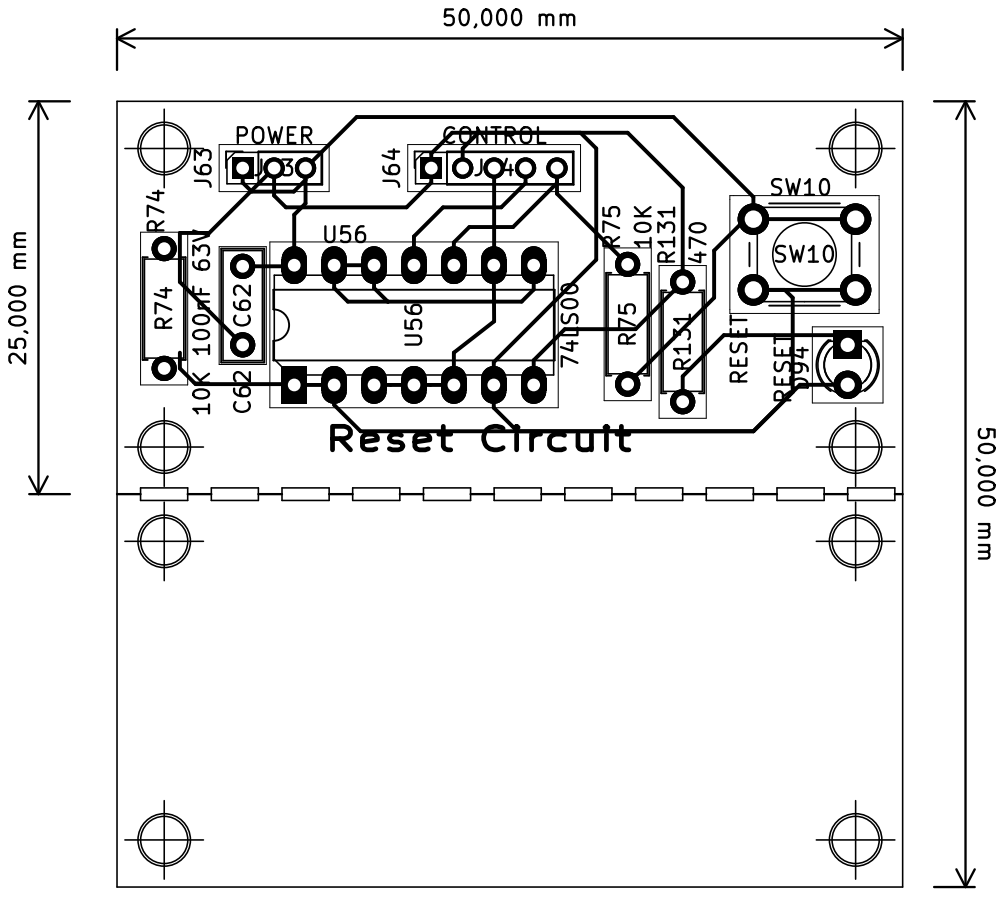
[picture p60: page 1]
