rick0x00/8bit-computer/HARDWARE/EDA/DOCUMENTS/Reset Circuit PCB.pdf

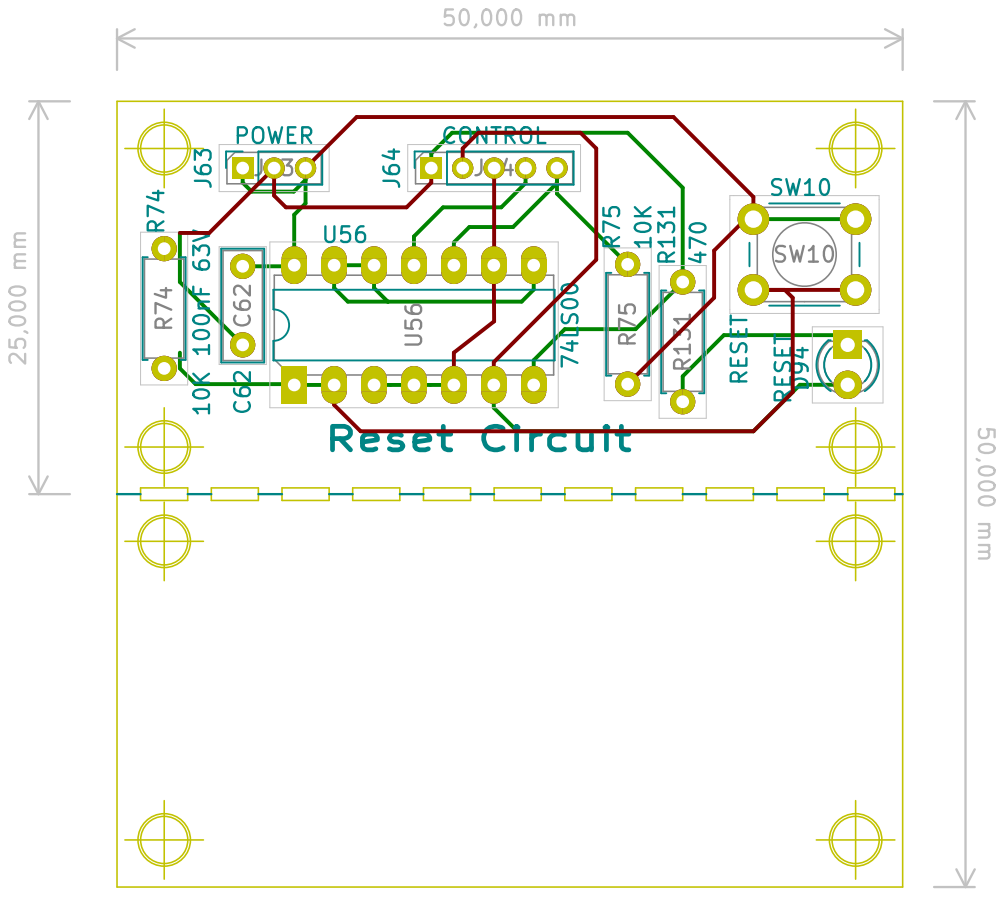
[picture p61: page 1]
