rick0x00/8bit-computer/HARDWARE/EDA/DOCUMENTS/Search And Execution Counter Black PCB.pdf

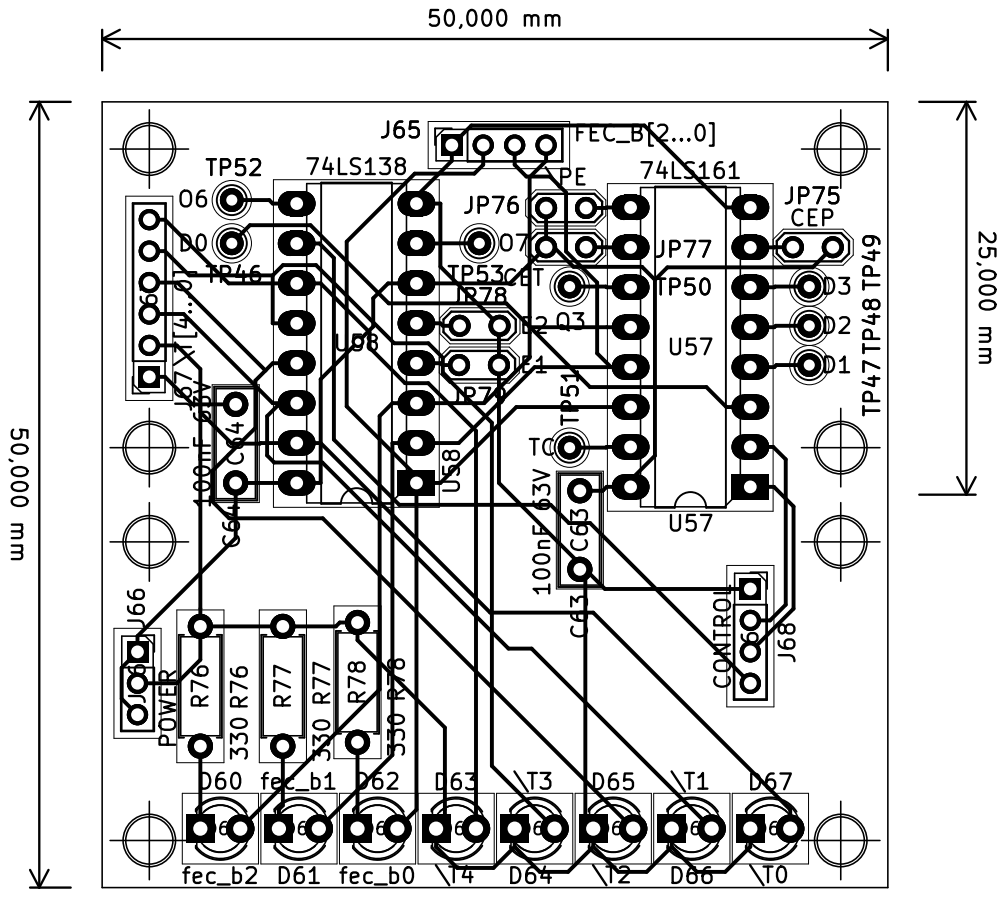
[picture p62: page 1]
