rick0x00/8bit-computer/HARDWARE/EDA/DOCUMENTS/Search And Execution Counter PCB.pdf

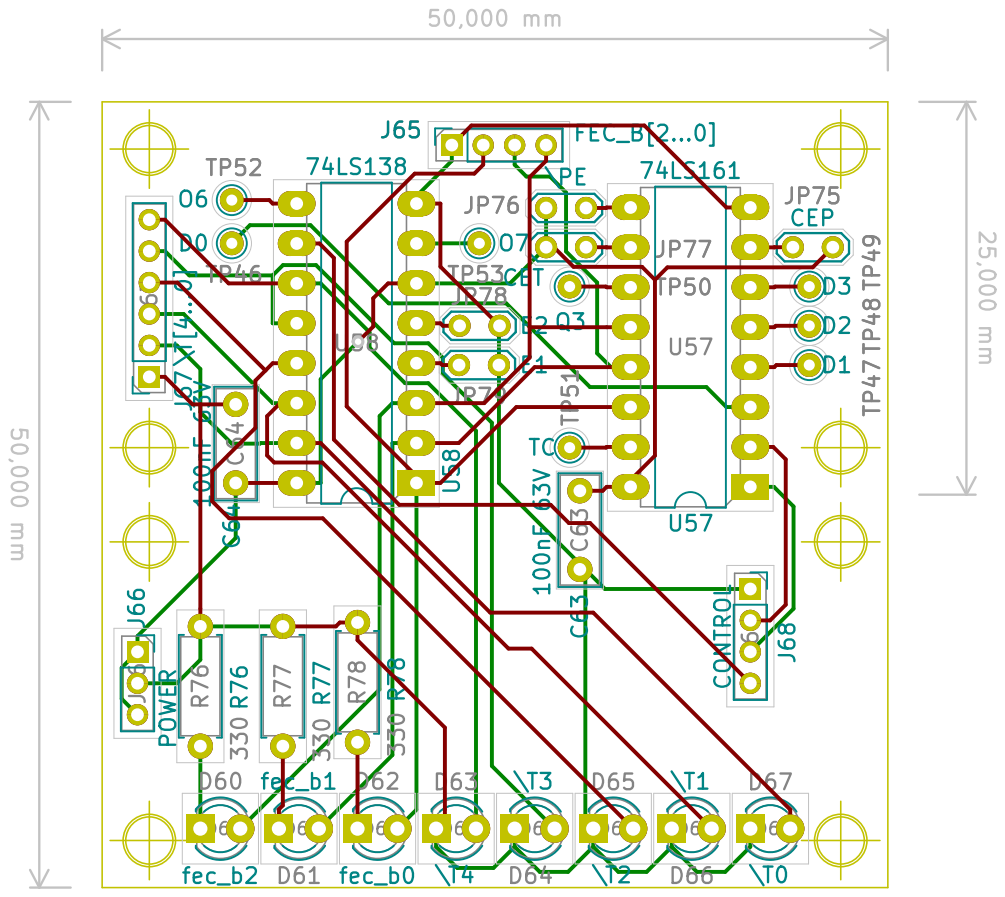
[picture p63: page 1]
