rick0x00/8bit-computer/HARDWARE/EDA/DOCUMENTS/Selection Circuit Black PCB.pdf

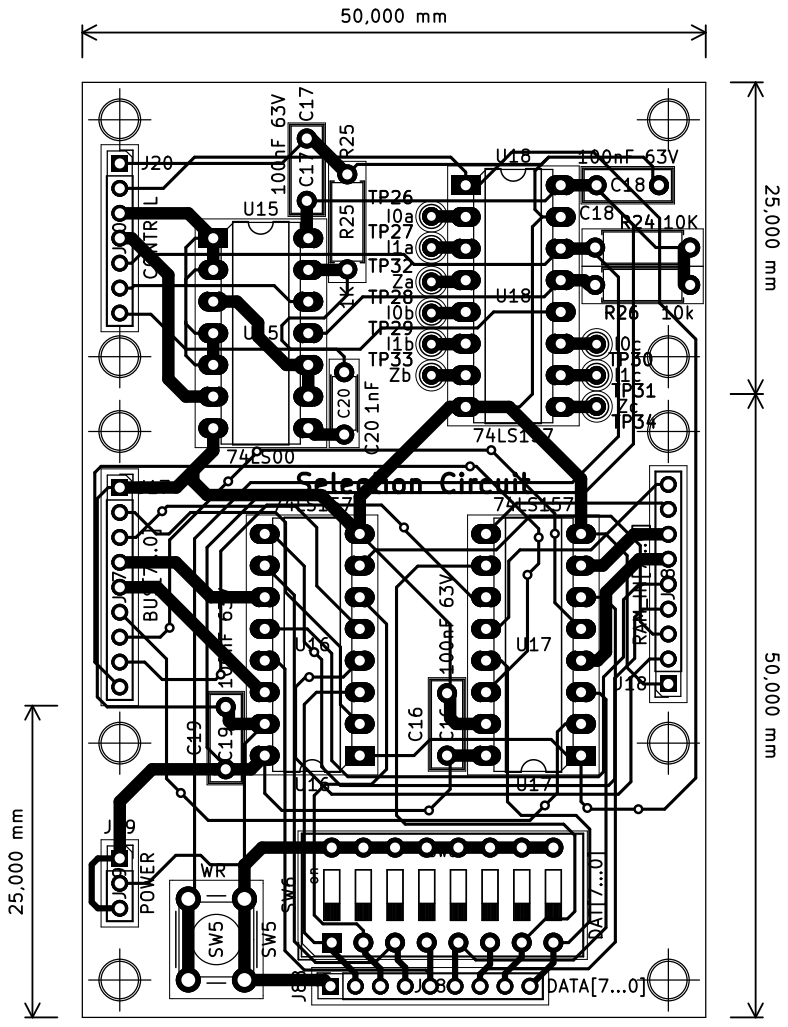
[picture p64: page 1]
