rick0x00/8bit-computer/HARDWARE/EDA/DOCUMENTS/Selection Circuit PCB.pdf

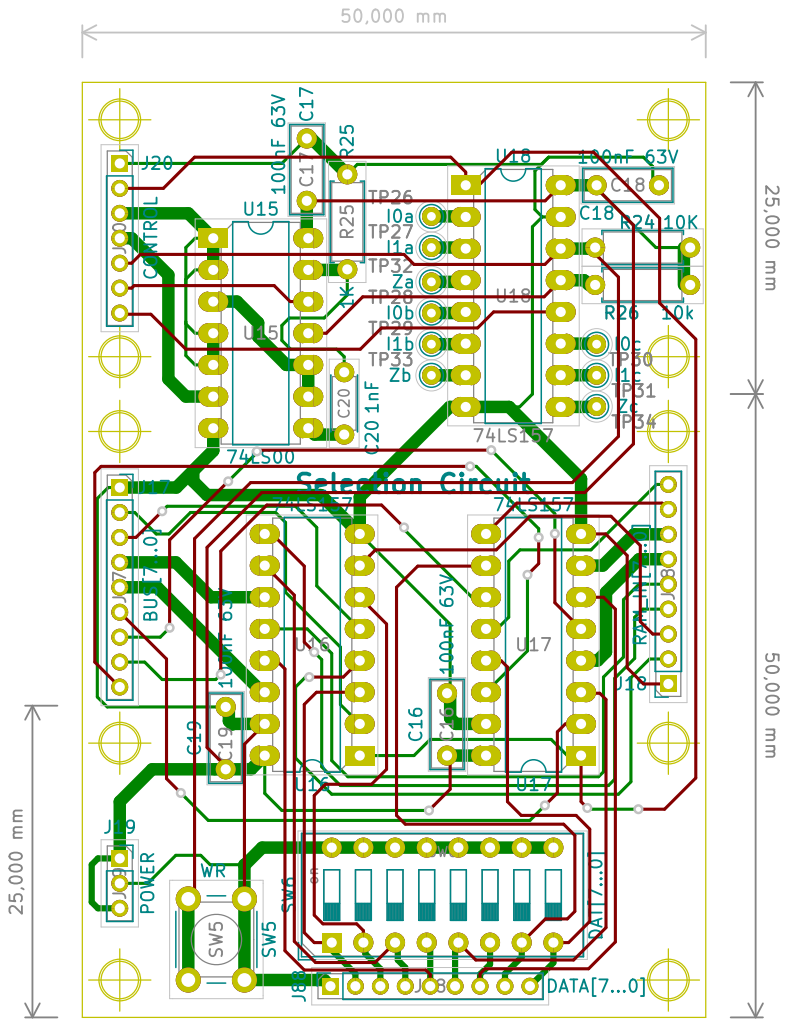
[picture p65: page 1]
