rick0x00/8bit-computer/HARDWARE/EDA/KiCad/8-bit computer/Arithmetic Unit.kicad_pcb

## KiCad design HARDWARE/EDA/KiCad/8-bit computer/Arithmetic Unit.kicad_pcb (2021-08-03)

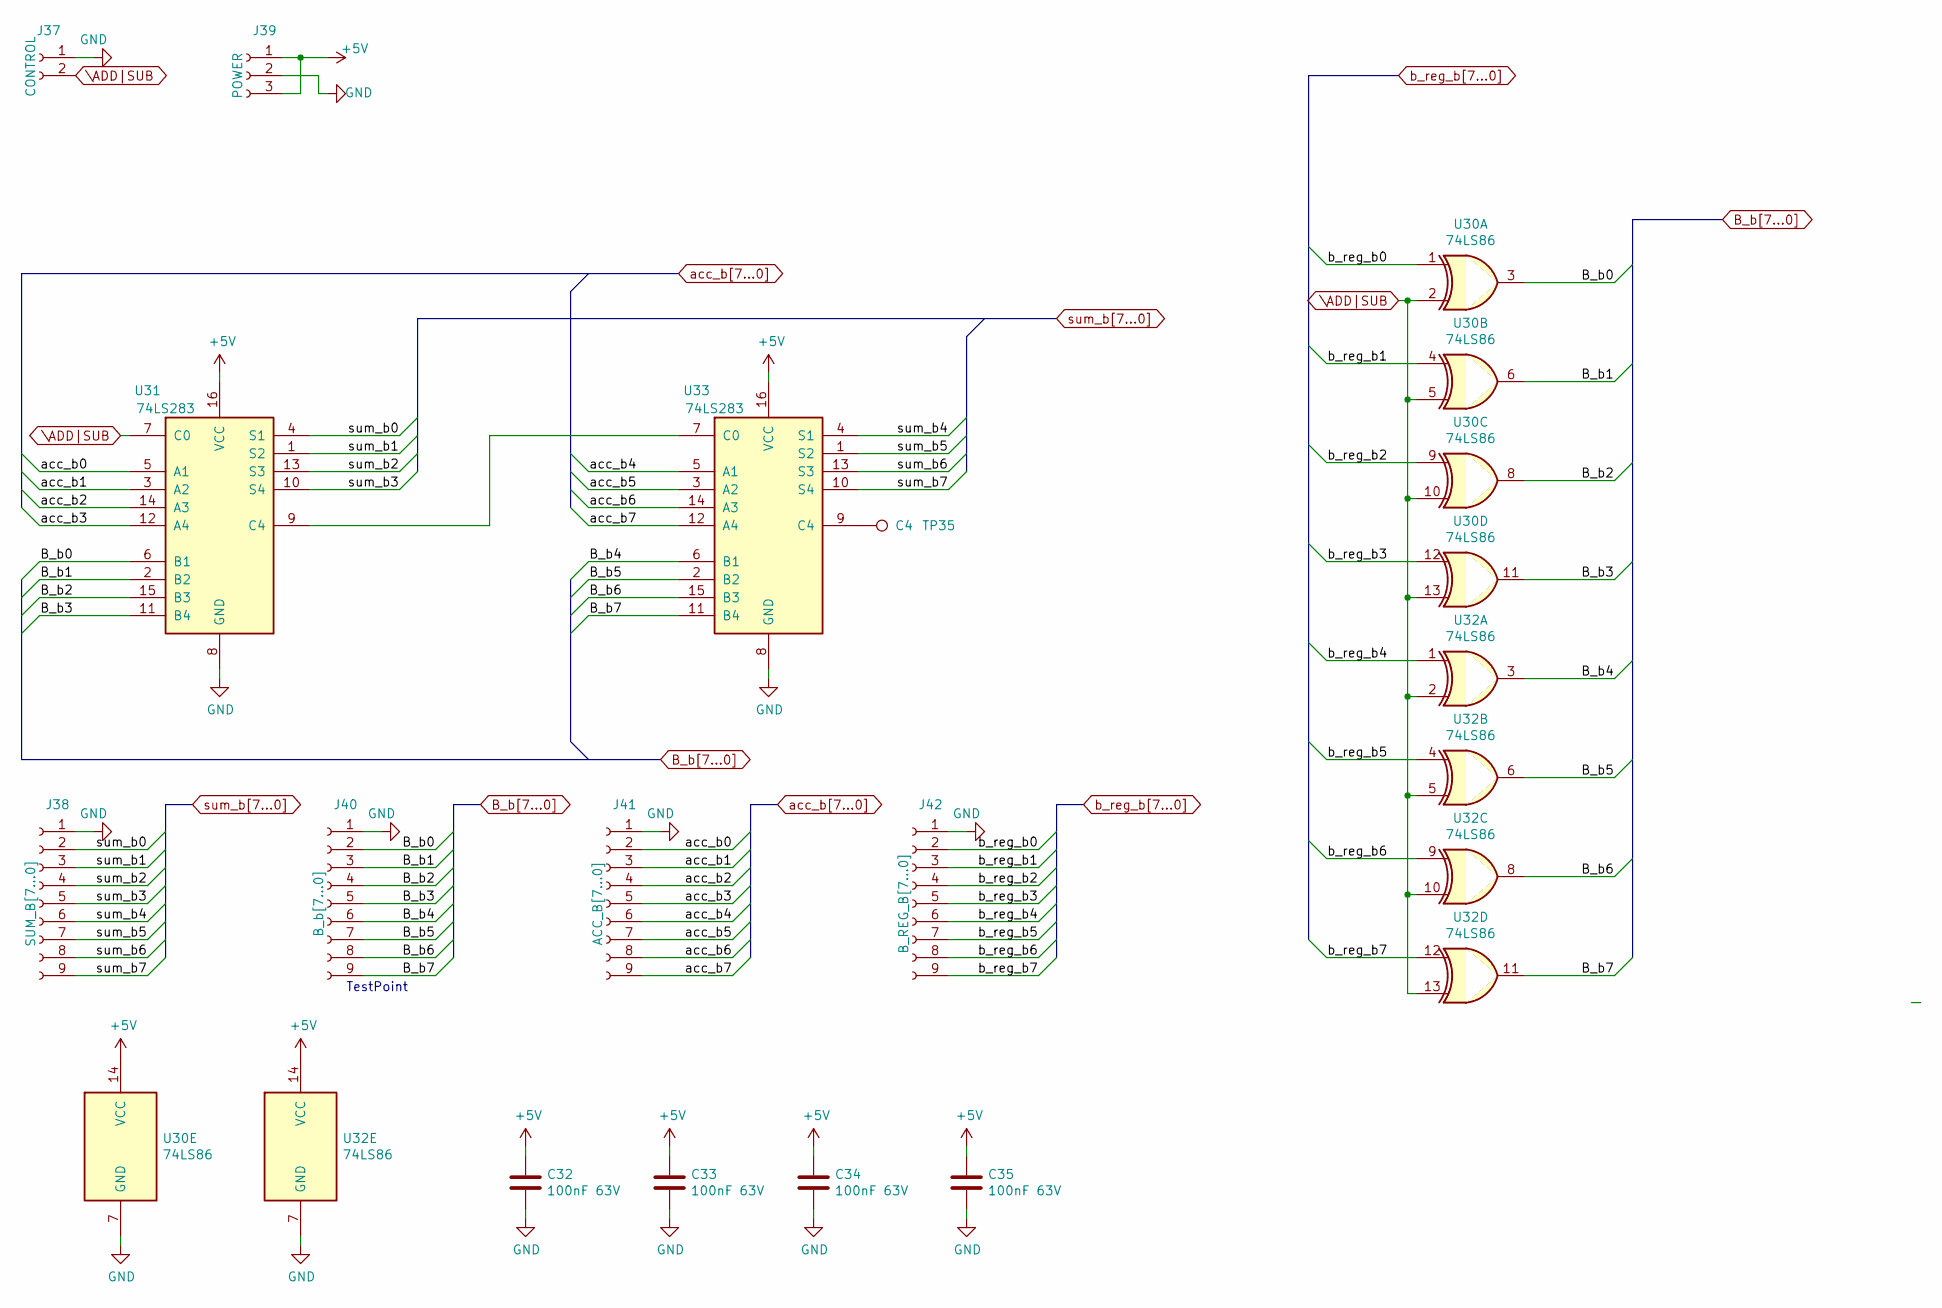
[picture p85: schematic Arithmetic Unit.sch]

Parts:
C32, C33, C34, C35: 100nF 63V; C_Rect_L7.0mm_W2.5mm_P5.00mm
J37: CONTROL; PinSocket_1x02_P2.00mm_Vertical
J38: SUM_B[7...0]; PinSocket_1x09_P2.00mm_Vertical
J39: POWER; PinSocket_1x03_P2.00mm_Vertical
J40: B_b[7...0]; PinSocket_1x09_P2.00mm_Vertical
J41: ACC_B[7...0]; PinSocket_1x09_P2.00mm_Vertical
J42: B_REG_B[7...0]; PinSocket_1x09_P2.00mm_Vertical
TP35: C4; TestPoint_THTPad_D1.5mm_Drill0.7mm
U30, U32: 74LS86; DIP-14_W7.62mm_LongPads
U31, U33: 74LS283; DIP-16_W7.62mm_LongPads

Connections:
+5V: C32.1, C33.1, C34.1, C35.1, J39.1, J39.3, U30.14 (VCC), U31.16 (VCC), U32.14 (VCC), U33.16 (VCC)
B_b0: J40.2, U30.3, U31.6 (B1)
B_b1: J40.3, U30.6, U31.2 (B2)
B_b2: J40.4, U30.8, U31.15 (B3)
B_b3: J40.5, U30.11, U31.11 (B4)
B_b4: J40.6, U32.3, U33.6 (B1)
B_b5: J40.7, U32.6, U33.2 (B2)
B_b6: J40.8, U32.8, U33.15 (B3)
B_b7: J40.9, U32.11, U33.11 (B4)
GND: C32.2, C33.2, C34.2, C35.2, J37.1, J38.1, J39.2, J40.1, J41.1, J42.1, U30.7 (GND), U31.8 (GND), U32.7 (GND), U33.8 (GND)
unnamed: TP35.1, U33.9 (C4)
unnamed: U31.9 (C4), U33.7 (C0)
\ADD|SUB: J37.2, U30.2, U30.5, U30.10, U30.13, U31.7 (C0), U32.2, U32.5, U32.10, U32.13
acc_b0: J41.2, U31.5 (A1)
acc_b1: J41.3, U31.3 (A2)
acc_b2: J41.4, U31.14 (A3)
acc_b3: J41.5, U31.12 (A4)
acc_b4: J41.6, U33.5 (A1)
acc_b5: J41.7, U33.3 (A2)
acc_b6: J41.8, U33.14 (A3)
acc_b7: J41.9, U33.12 (A4)
b_reg_b0: J42.2, U30.1
b_reg_b1: J42.3, U30.4
b_reg_b2: J42.4, U30.9
b_reg_b3: J42.5, U30.12
b_reg_b4: J42.6, U32.1
b_reg_b5: J42.7, U32.4
b_reg_b6: J42.8, U32.9
b_reg_b7: J42.9, U32.12
sum_b0: J38.2, U31.4 (S1)
sum_b1: J38.3, U31.1 (S2)
sum_b2: J38.4, U31.13 (S3)
sum_b3: J38.5, U31.10 (S4)
sum_b4: J38.6, U33.4 (S1)
sum_b5: J38.7, U33.1 (S2)
sum_b6: J38.8, U33.13 (S3)
sum_b7: J38.9, U33.10 (S4)

Notes on the sheet:
TestPoint

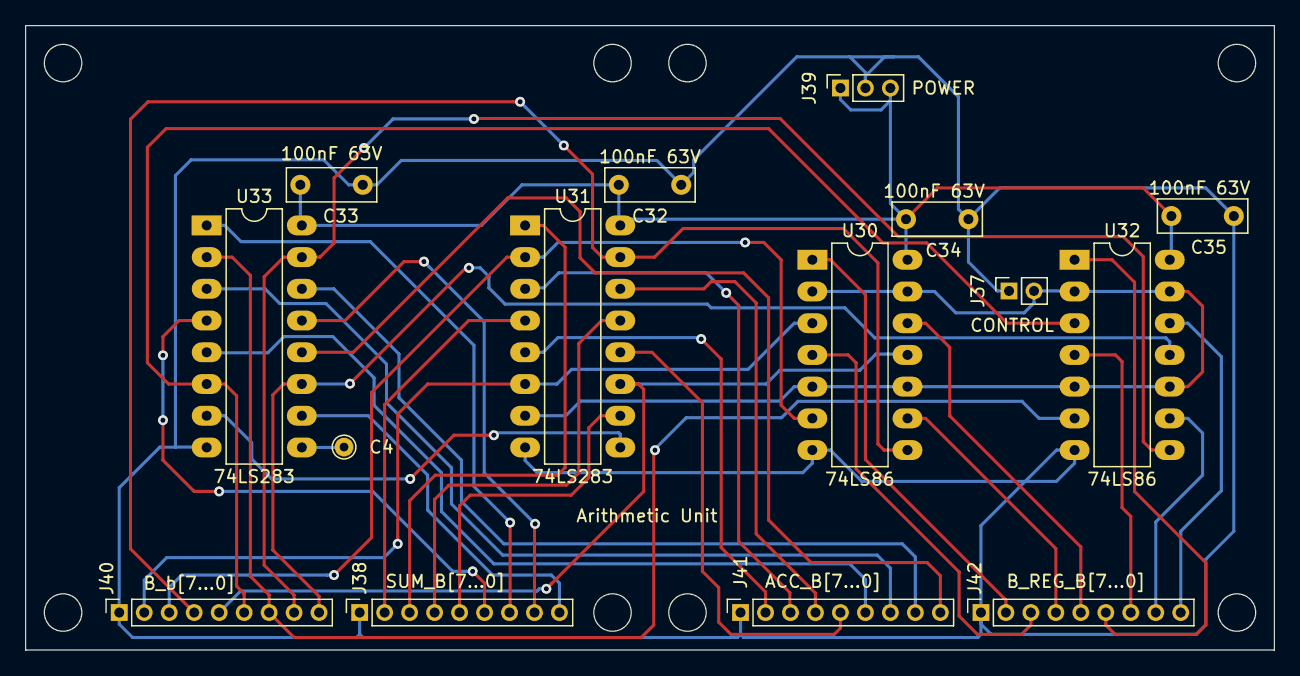
[picture p86: board Arithmetic Unit.kicad_pcb from above]

Board: 2 copper layers, 100.0 x 50.0 mm, 15 parts (0 on the bottom side), 37 nets.
