rick0x00/8bit-computer/HARDWARE/EDA/KiCad/8-bit computer/Bus Simulator.kicad_pcb

## KiCad design HARDWARE/EDA/KiCad/8-bit computer/Bus Simulator.kicad_pcb (2021-08-03)

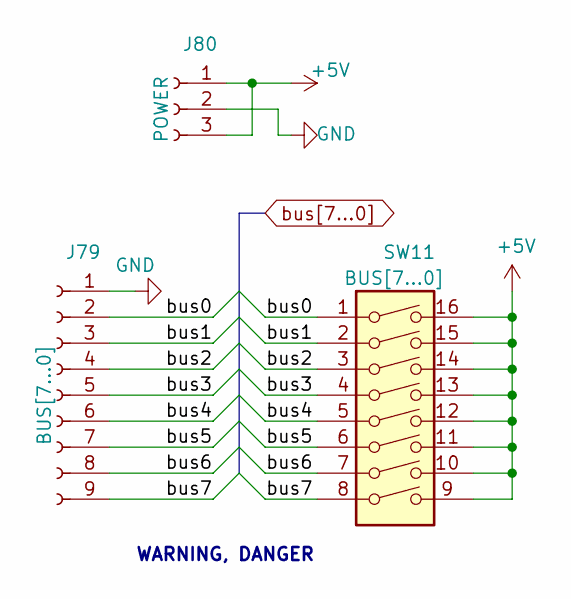
[picture p87: schematic Bus Simulator.sch]

Parts:
J79: BUS[7...0]; PinSocket_1x09_P2.00mm_Vertical
J80: POWER; PinSocket_1x03_P2.00mm_Vertical
SW11: BUS[7...0]; SW_DIP_SPSTx08_Slide_9.78x22.5mm_W7.62mm_P2.54mm

Connections:
+5V: J80.1, J80.3, SW11.9, SW11.10, SW11.11, SW11.12, SW11.13, SW11.14, SW11.15, SW11.16
GND: J79.1, J80.2
bus0: J79.2, SW11.1
bus1: J79.3, SW11.2
bus2: J79.4, SW11.3
bus3: J79.5, SW11.4
bus4: J79.6, SW11.5
bus5: J79.7, SW11.6
bus6: J79.8, SW11.7
bus7: J79.9, SW11.8

Notes on the sheet:
WARNING, DANGER

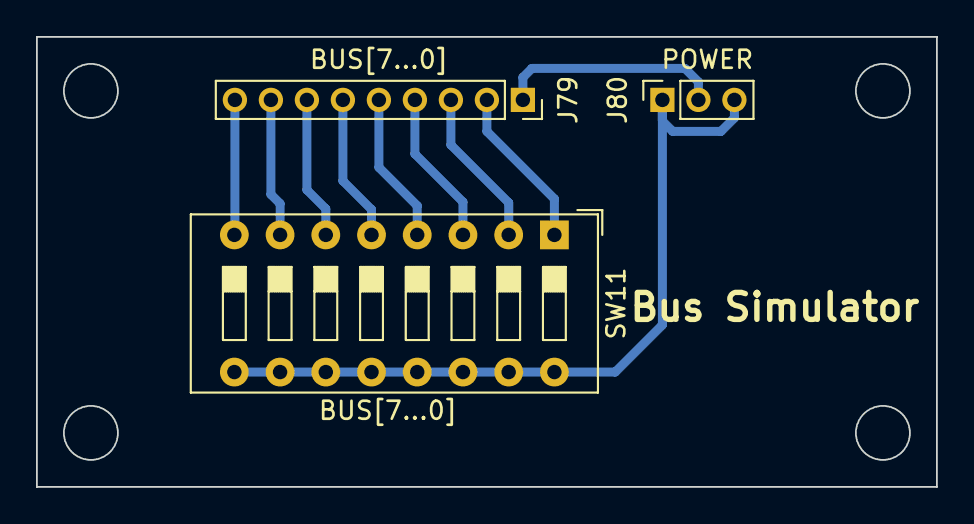
[picture p88: board Bus Simulator.kicad_pcb from above]

Board: 2 copper layers, 50.0 x 25.0 mm, 3 parts (0 on the bottom side), 10 nets.
