rick0x00/8bit-computer/HARDWARE/EDA/KiCad/8-bit computer/Control Word.kicad_pcb

## KiCad design HARDWARE/EDA/KiCad/8-bit computer/Control Word.kicad_pcb (2021-08-03)

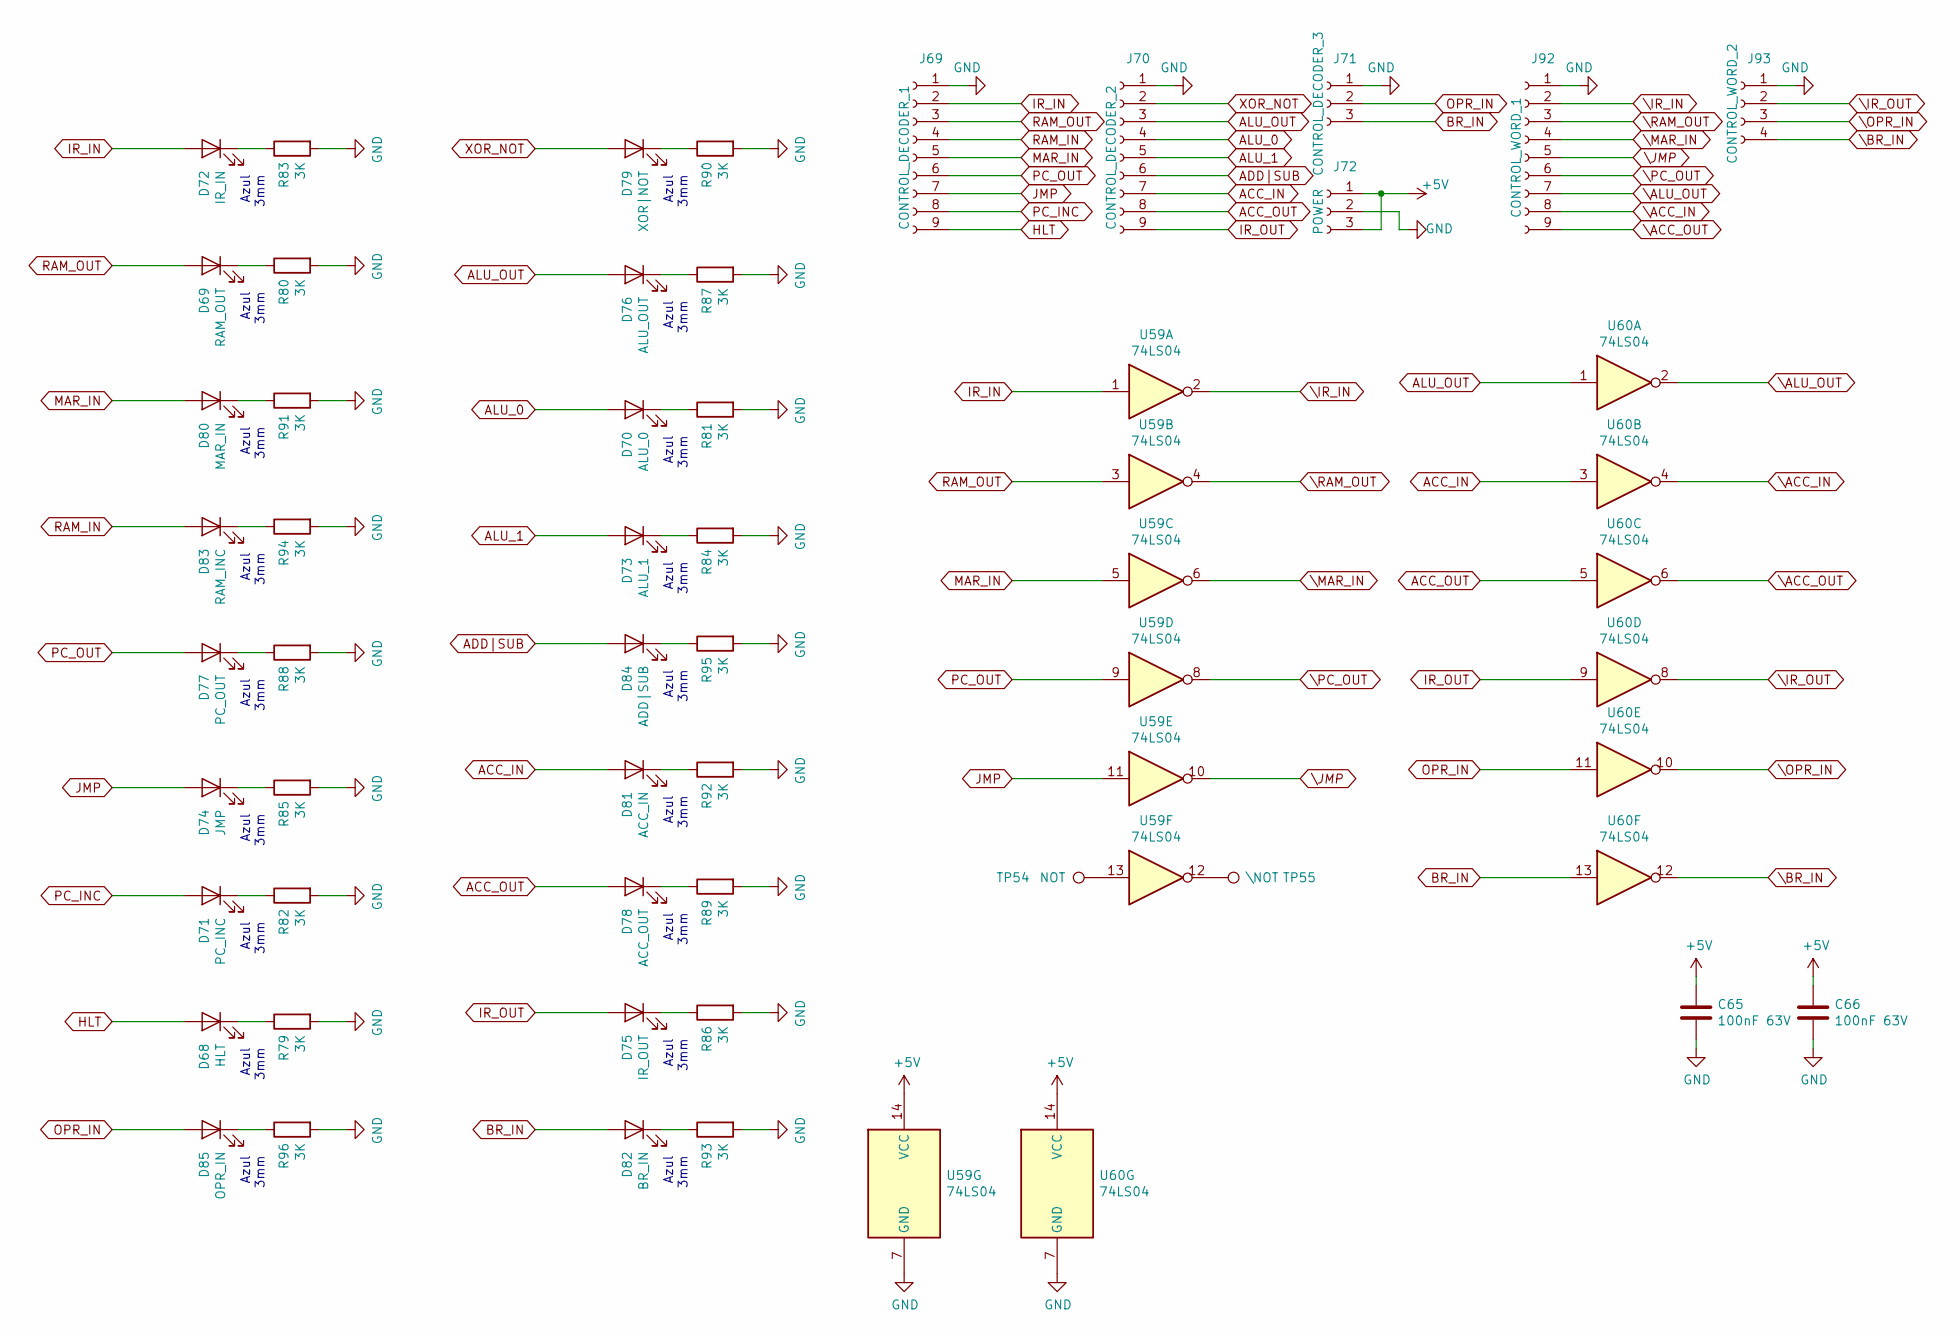
[picture p89: schematic Control Word.sch]

Parts:
C65, C66: 100nF 63V; C_Rect_L7.0mm_W2.5mm_P5.00mm
D68: HLT; LED_D3.0mm_Clear
D69: RAM_OUT; LED_D3.0mm_Clear
D70: ALU_0; LED_D3.0mm_Clear
D71: PC_INC; LED_D3.0mm_Clear
D72: IR_IN; LED_D3.0mm_Clear
D73: ALU_1; LED_D3.0mm_Clear
D74: JMP; LED_D3.0mm_Clear
D75: IR_OUT; LED_D3.0mm_Clear
D76: ALU_OUT; LED_D3.0mm_Clear
D77: PC_OUT; LED_D3.0mm_Clear
D78: ACC_OUT; LED_D3.0mm_Clear
D79: XOR|NOT; LED_D3.0mm_Clear
D80: MAR_IN; LED_D3.0mm_Clear
D81: ACC_IN; LED_D3.0mm_Clear
D82: BR_IN; LED_D3.0mm_Clear
D83: RAM_INC; LED_D3.0mm_Clear
D84: ADD|SUB; LED_D3.0mm_Clear
D85: OPR_IN; LED_D3.0mm_Clear
J69: CONTROL_DECODER_1; PinSocket_1x09_P2.00mm_Vertical
J70: CONTROL_DECODER_2; PinSocket_1x09_P2.00mm_Vertical
J71: CONTROL_DECODER_3; PinSocket_1x03_P2.00mm_Vertical
J72: POWER; PinSocket_1x03_P2.00mm_Vertical
J92: CONTROL_WORD_1; PinSocket_1x09_P2.00mm_Vertical
J93: CONTROL_WORD_2; PinSocket_1x04_P2.00mm_Vertical
R79, R80, R81, R82, R83, R84, R85, R86, R87, R88, R89, R90, R91, R92, R93, R94, R95, R96: 3K; R_Axial_DIN0207_L6.3mm_D2.5mm_P7.62mm_Horizontal
TP54: NOT; TestPoint_THTPad_D1.5mm_Drill0.7mm
TP55: \\NOT; TestPoint_THTPad_D1.5mm_Drill0.7mm
U59, U60: 74LS04; DIP-14_W7.62mm_LongPads

Connections:
+5V: C65.1, C66.1, J72.1, J72.3, U59.14 (VCC), U60.14 (VCC)
ACC_IN: D81.2 (A), J70.7, U60.3
ACC_OUT: D78.2 (A), J70.8, U60.5
ADD|SUB: D84.2 (A), J70.6
ALU_0: D70.2 (A), J70.4
ALU_1: D73.2 (A), J70.5
ALU_OUT: D76.2 (A), J70.3, U60.1
BR_IN: D82.2 (A), J71.3, U60.13
GND: C65.2, C66.2, J69.1, J70.1, J71.1, J72.2, J92.1, J93.1, R79.2, R80.2, R81.2, R82.2, R83.2, R84.2, R85.2, R86.2, R87.2, R88.2, R89.2, R90.2, R91.2, R92.2, R93.2, R94.2, R95.2, R96.2, U59.7 (GND), U60.7 (GND)
HLT: D68.2 (A), J69.9
IR_IN: D72.2 (A), J69.2, U59.1
IR_OUT: D75.2 (A), J70.9, U60.9
JMP: D74.2 (A), J69.7, U59.11
MAR_IN: D80.2 (A), J69.5, U59.5
unnamed: D68.1 (K), R79.1
unnamed: D69.1 (K), R80.1
unnamed: D70.1 (K), R81.1
unnamed: D71.1 (K), R82.1
unnamed: D72.1 (K), R83.1
unnamed: D73.1 (K), R84.1
unnamed: D74.1 (K), R85.1
unnamed: D75.1 (K), R86.1
unnamed: D76.1 (K), R87.1
unnamed: D77.1 (K), R88.1
unnamed: D78.1 (K), R89.1
unnamed: D79.1 (K), R90.1
unnamed: D80.1 (K), R91.1
unnamed: D81.1 (K), R92.1
unnamed: D82.1 (K), R93.1
unnamed: D83.1 (K), R94.1
unnamed: D84.1 (K), R95.1
unnamed: D85.1 (K), R96.1
unnamed: TP54.1, U59.13
unnamed: TP55.1, U59.12
OPR_IN: D85.2 (A), J71.2, U60.11
PC_INC: D71.2 (A), J69.8
PC_OUT: D77.2 (A), J69.6, U59.9
RAM_IN: D83.2 (A), J69.4
RAM_OUT: D69.2 (A), J69.3, U59.3
XOR_NOT: D79.2 (A), J70.2
\ACC_IN: J92.8, U60.4
\ACC_OUT: J92.9, U60.6
\ALU_OUT: J92.7, U60.2
\BR_IN: J93.4, U60.12
\IR_IN: J92.2, U59.2
\IR_OUT: J93.2, U60.8
\JMP: J92.5, U59.10
\MAR_IN: J92.4, U59.6
\OPR_IN: J93.3, U60.10
\PC_OUT: J92.6, U59.8
\RAM_OUT: J92.3, U59.4

Notes on the sheet:
Azul 3mm

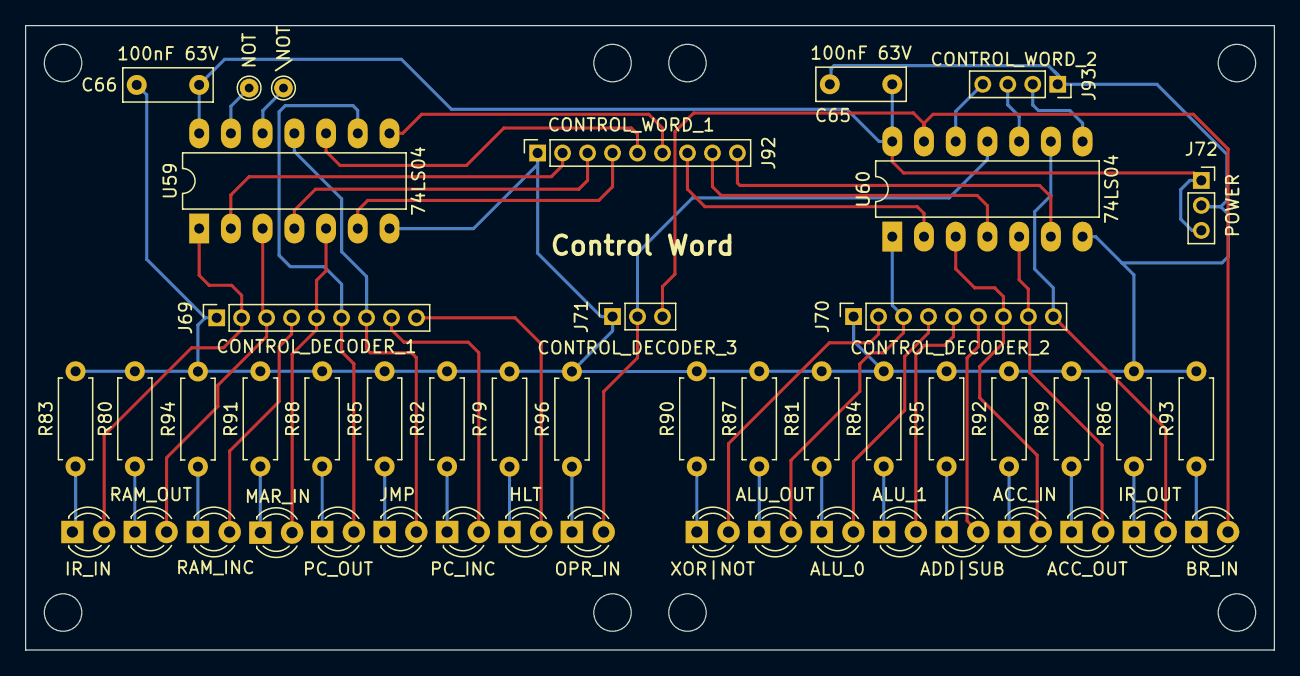
[picture p90: board Control Word.kicad_pcb from above]

Board: 2 copper layers, 100.0 x 50.0 mm, 48 parts (0 on the bottom side), 51 nets.
