rick0x00/8bit-computer/HARDWARE/EDA/KiCad/8-bit computer/Output Register.kicad_pcb

## KiCad design HARDWARE/EDA/KiCad/8-bit computer/Output Register.kicad_pcb (2021-08-03)

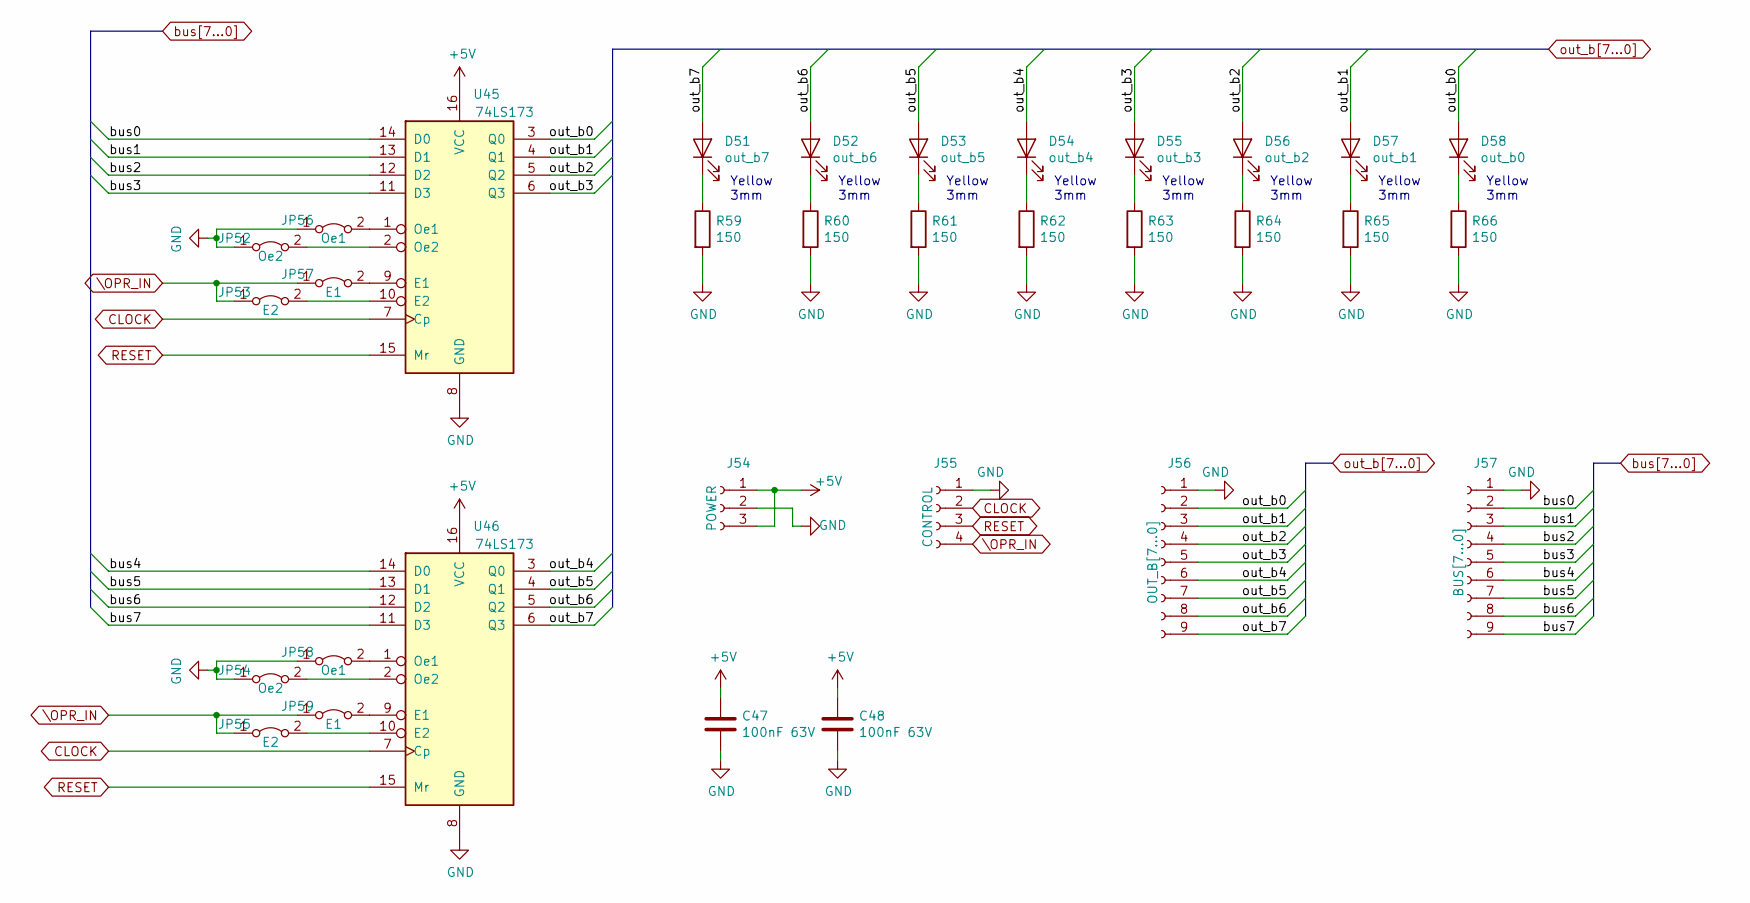
[picture p91: schematic Output Register.sch]

Parts:
C47, C48: 100nF 63V; C_Rect_L7.0mm_W2.5mm_P5.00mm
D51: out_b7; LED_D3.0mm_Clear
D52: out_b6; LED_D3.0mm_Clear
D53: out_b5; LED_D3.0mm_Clear
D54: out_b4; LED_D3.0mm_Clear
D55: out_b3; LED_D3.0mm_Clear
D56: out_b2; LED_D3.0mm_Clear
D57: out_b1; LED_D3.0mm_Clear
D58: out_b0; LED_D3.0mm_Clear
J54: POWER; PinSocket_1x03_P2.00mm_Vertical
J55: CONTROL; PinSocket_1x04_P2.00mm_Vertical
J56: OUT_B[7...0]; PinSocket_1x09_P2.00mm_Vertical
J57: BUS[7...0]; PinSocket_1x09_P2.00mm_Vertical
JP52, JP54: Oe2; TestPoint_2Pads_Pitch2.54mm_Drill0.8mm
JP53, JP55: E2; TestPoint_2Pads_Pitch2.54mm_Drill0.8mm
JP56, JP58: Oe1; TestPoint_2Pads_Pitch2.54mm_Drill0.8mm
JP57, JP59: E1; TestPoint_2Pads_Pitch2.54mm_Drill0.8mm
R59, R60, R61, R62, R63, R64, R65, R66: 150; R_Axial_DIN0207_L6.3mm_D2.5mm_P7.62mm_Horizontal
U45, U46: 74LS173; DIP-16_W7.62mm_LongPads

Connections:
+5V: C47.1, C48.1, J54.1, J54.3, U45.16 (VCC), U46.16 (VCC)
CLOCK: J55.2, U45.7 (Cp), U46.7 (Cp)
GND: C47.2, C48.2, J54.2, J55.1, J56.1, J57.1, JP52.1 (A), JP54.1 (A), JP56.1 (A), JP58.1 (A), R59.2, R60.2, R61.2, R62.2, R63.2, R64.2, R65.2, R66.2, U45.8 (GND), U46.8 (GND)
unnamed: D51.1 (K), R59.1
unnamed: D52.1 (K), R60.1
unnamed: D53.1 (K), R61.1
unnamed: D54.1 (K), R62.1
unnamed: D55.1 (K), R63.1
unnamed: D56.1 (K), R64.1
unnamed: D57.1 (K), R65.1
unnamed: D58.1 (K), R66.1
unnamed: JP52.2 (B), U45.2 (Oe2)
unnamed: JP53.2 (B), U45.10 (E2)
unnamed: JP54.2 (B), U46.2 (Oe2)
unnamed: JP55.2 (B), U46.10 (E2)
unnamed: JP56.2 (B), U45.1 (Oe1)
unnamed: JP57.2 (B), U45.9 (E1)
unnamed: JP58.2 (B), U46.1 (Oe1)
unnamed: JP59.2 (B), U46.9 (E1)
RESET: J55.3, U45.15 (Mr), U46.15 (Mr)
\OPR_IN: J55.4, JP53.1 (A), JP55.1 (A), JP57.1 (A), JP59.1 (A)
bus0: J57.2, U45.14 (D0)
bus1: J57.3, U45.13 (D1)
bus2: J57.4, U45.12 (D2)
bus3: J57.5, U45.11 (D3)
bus4: J57.6, U46.14 (D0)
bus5: J57.7, U46.13 (D1)
bus6: J57.8, U46.12 (D2)
bus7: J57.9, U46.11 (D3)
out_b0: D58.2 (A), J56.2, U45.3 (Q0)
out_b1: D57.2 (A), J56.3, U45.4 (Q1)
out_b2: D56.2 (A), J56.4, U45.5 (Q2)
out_b3: D55.2 (A), J56.5, U45.6 (Q3)
out_b4: D54.2 (A), J56.6, U46.3 (Q0)
out_b5: D53.2 (A), J56.7, U46.4 (Q1)
out_b6: D52.2 (A), J56.8, U46.5 (Q2)
out_b7: D51.2 (A), J56.9, U46.6 (Q3)

Notes on the sheet:
Yellow 3mm

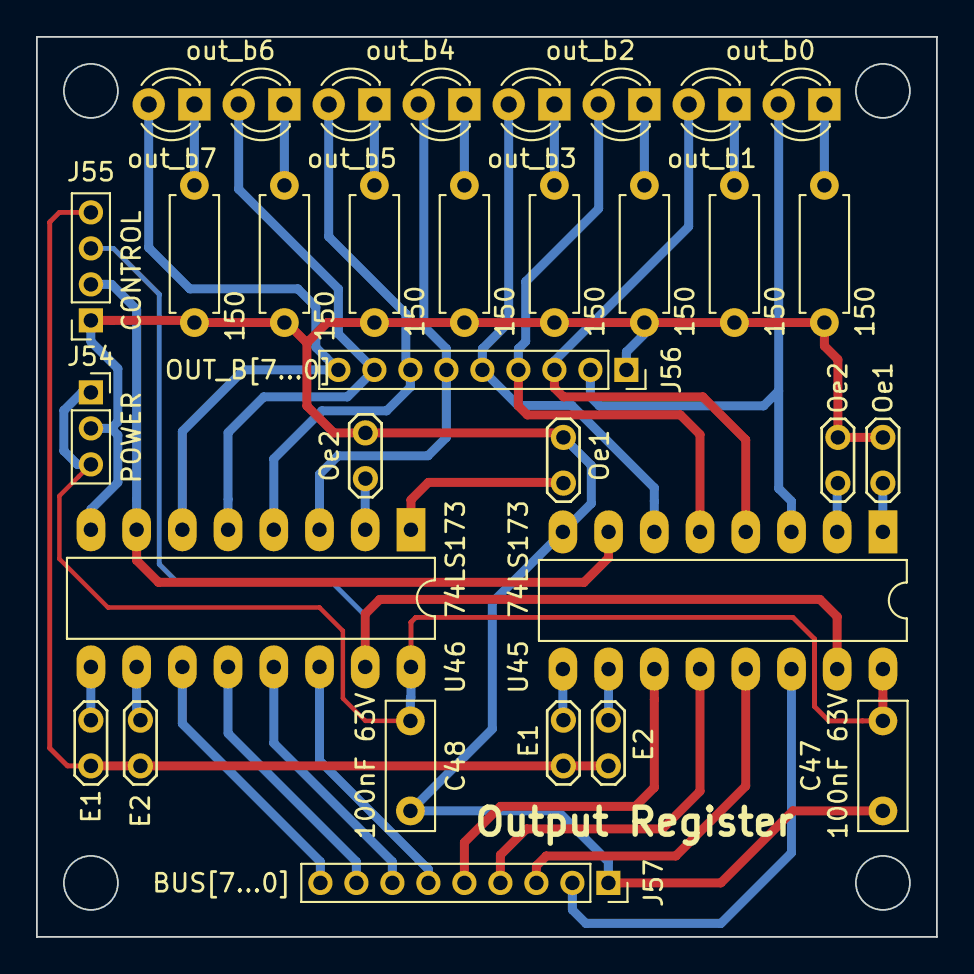
[picture p92: board Output Register.kicad_pcb from above]

Board: 2 copper layers, 50.0 x 50.0 mm, 32 parts (0 on the bottom side), 37 nets.
