rick0x00/8bit-computer/HARDWARE/EDA/KiCad/8-bit computer/Control Decoder.kicad_pcb

## KiCad design HARDWARE/EDA/KiCad/8-bit computer/Control Decoder.kicad_pcb (2021-08-03)

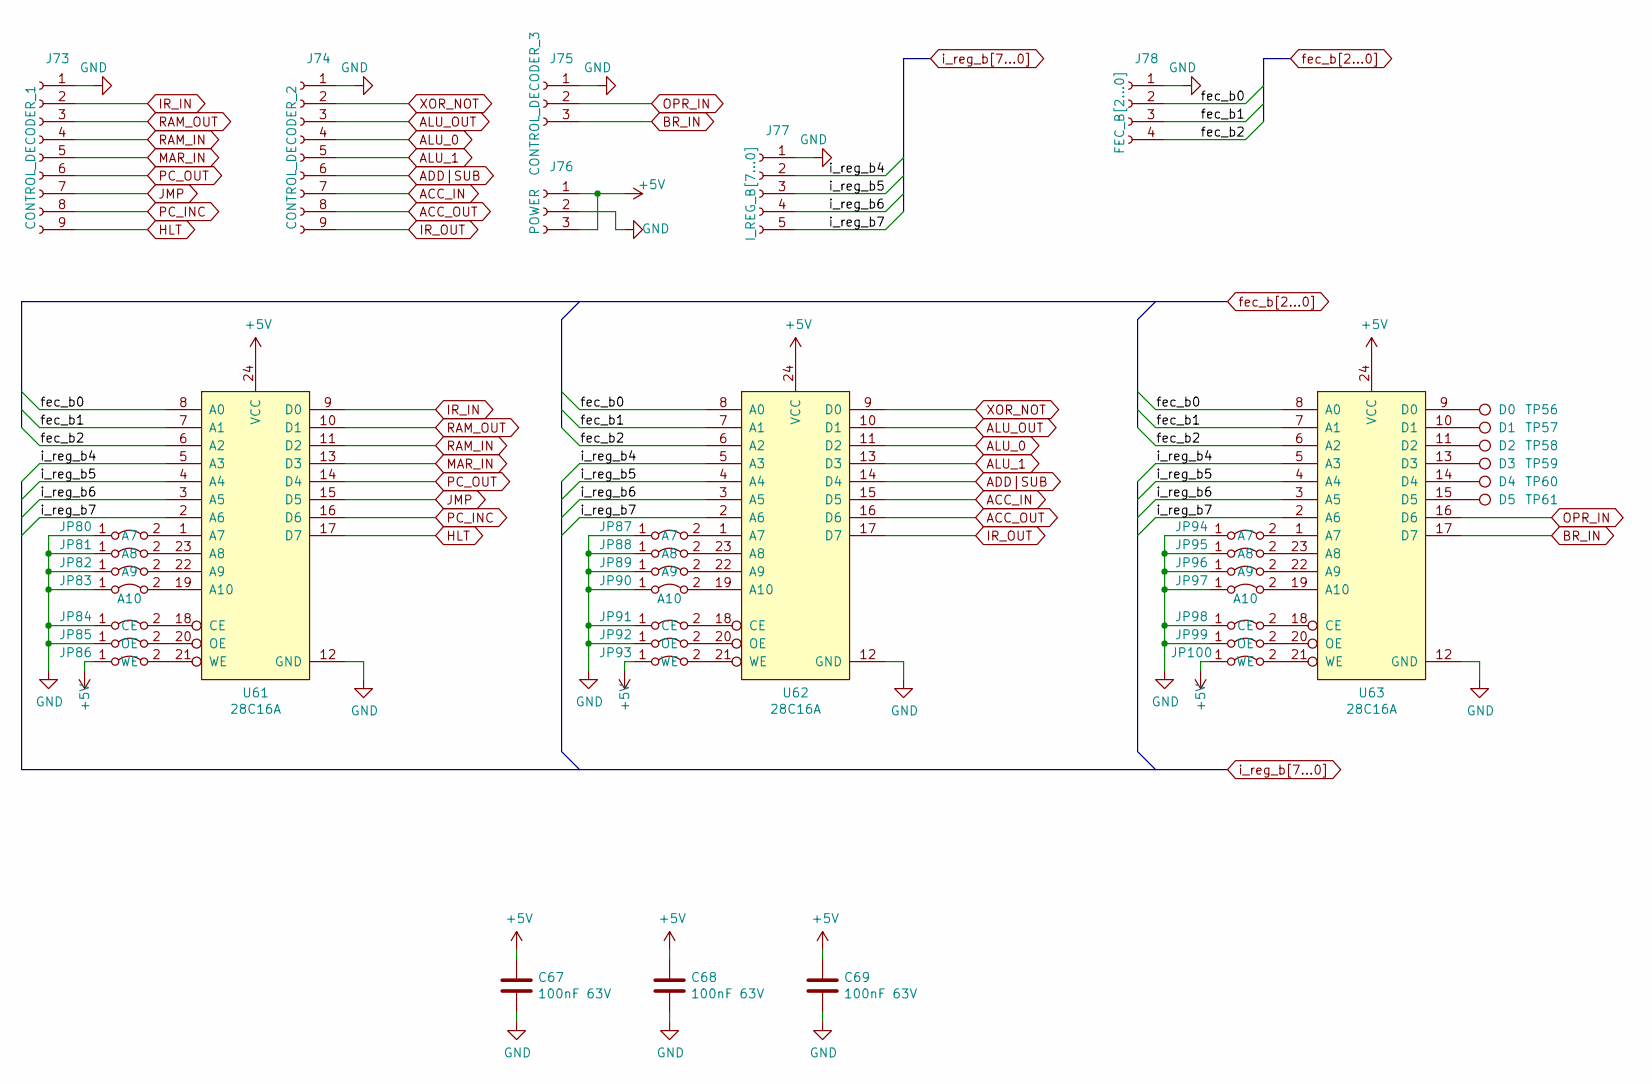
[picture p93: schematic Control Decoder.sch]

Parts:
C67, C68, C69: 100nF 63V; C_Rect_L7.0mm_W2.5mm_P5.00mm
J73: CONTROL_DECODER_1; PinSocket_1x09_P2.00mm_Vertical
J74: CONTROL_DECODER_2; PinSocket_1x09_P2.00mm_Vertical
J75: CONTROL_DECODER_3; PinSocket_1x03_P2.00mm_Vertical
J76: POWER; PinSocket_1x03_P2.00mm_Vertical
J77: I_REG_B[7...0]; PinSocket_1x05_P2.00mm_Vertical
J78: FEC_B[2...0]; PinSocket_1x04_P2.00mm_Vertical
JP80, JP87, JP94: A7; TestPoint_2Pads_Pitch2.54mm_Drill0.8mm
JP81, JP88, JP95: A8; TestPoint_2Pads_Pitch2.54mm_Drill0.8mm
JP82, JP89, JP96: A9; TestPoint_2Pads_Pitch2.54mm_Drill0.8mm
JP83, JP90, JP97: A10; TestPoint_2Pads_Pitch2.54mm_Drill0.8mm
JP84, JP91, JP98: CE; TestPoint_2Pads_Pitch2.54mm_Drill0.8mm
JP85, JP92, JP99: OE; TestPoint_2Pads_Pitch2.54mm_Drill0.8mm
JP86, JP93, JP100: WE; TestPoint_2Pads_Pitch2.54mm_Drill0.8mm
TP56: D0; TestPoint_THTPad_D1.5mm_Drill0.7mm
TP57: D1; TestPoint_THTPad_D1.5mm_Drill0.7mm
TP58: D2; TestPoint_THTPad_D1.5mm_Drill0.7mm
TP59: D3; TestPoint_THTPad_D1.5mm_Drill0.7mm
TP60: D4; TestPoint_THTPad_D1.5mm_Drill0.7mm
TP61: D5; TestPoint_THTPad_D1.5mm_Drill0.7mm
U61, U62, U63: 28C16A; DIP-24_W15.24mm_LongPads

Connections:
+5V: C67.1, C68.1, C69.1, J76.1, J76.3, JP86.1 (A), JP93.1 (A), JP100.1 (A), U61.24 (VCC), U62.24 (VCC), U63.24 (VCC)
ACC_IN: J74.7, U62.15 (D5)
ACC_OUT: J74.8, U62.16 (D6)
ADD|SUB: J74.6, U62.14 (D4)
ALU_0: J74.4, U62.11 (D2)
ALU_1: J74.5, U62.13 (D3)
ALU_OUT: J74.3, U62.10 (D1)
BR_IN: J75.3, U63.17 (D7)
GND: C67.2, C68.2, C69.2, J73.1, J74.1, J75.1, J76.2, J77.1, J78.1, JP80.1 (A), JP81.1 (A), JP82.1 (A), JP83.1 (A), JP84.1 (A), JP85.1 (A), JP87.1 (A), JP88.1 (A), JP89.1 (A), JP90.1 (A), JP91.1 (A), JP92.1 (A), JP94.1 (A), JP95.1 (A), JP96.1 (A), JP97.1 (A), JP98.1 (A), JP99.1 (A), U61.12 (GND), U62.12 (GND), U63.12 (GND)
HLT: J73.9, U61.17 (D7)
IR_IN: J73.2, U61.9 (D0)
IR_OUT: J74.9, U62.17 (D7)
JMP: J73.7, U61.15 (D5)
MAR_IN: J73.5, U61.13 (D3)
unnamed: JP80.2 (B), U61.1 (A7)
unnamed: JP81.2 (B), U61.23 (A8)
unnamed: JP82.2 (B), U61.22 (A9)
unnamed: JP83.2 (B), U61.19 (A10)
unnamed: JP84.2 (B), U61.18 (CE)
unnamed: JP85.2 (B), U61.20 (OE)
unnamed: JP86.2 (B), U61.21 (WE)
unnamed: JP87.2 (B), U62.1 (A7)
unnamed: JP88.2 (B), U62.23 (A8)
unnamed: JP89.2 (B), U62.22 (A9)
unnamed: JP90.2 (B), U62.19 (A10)
unnamed: JP91.2 (B), U62.18 (CE)
unnamed: JP92.2 (B), U62.20 (OE)
unnamed: JP93.2 (B), U62.21 (WE)
unnamed: JP94.2 (B), U63.1 (A7)
unnamed: JP95.2 (B), U63.23 (A8)
unnamed: JP96.2 (B), U63.22 (A9)
unnamed: JP97.2 (B), U63.19 (A10)
unnamed: JP98.2 (B), U63.18 (CE)
unnamed: JP99.2 (B), U63.20 (OE)
unnamed: JP100.2 (B), U63.21 (WE)
unnamed: TP56.1, U63.9 (D0)
unnamed: TP57.1, U63.10 (D1)
unnamed: TP58.1, U63.11 (D2)
unnamed: TP59.1, U63.13 (D3)
unnamed: TP60.1, U63.14 (D4)
unnamed: TP61.1, U63.15 (D5)
OPR_IN: J75.2, U63.16 (D6)
PC_INC: J73.8, U61.16 (D6)
PC_OUT: J73.6, U61.14 (D4)
RAM_IN: J73.4, U61.11 (D2)
RAM_OUT: J73.3, U61.10 (D1)
XOR_NOT: J74.2, U62.9 (D0)
fec_b0: J78.2, U61.8 (A0), U62.8 (A0), U63.8 (A0)
fec_b1: J78.3, U61.7 (A1), U62.7 (A1), U63.7 (A1)
fec_b2: J78.4, U61.6 (A2), U62.6 (A2), U63.6 (A2)
i_reg_b4: J77.2, U61.5 (A3), U62.5 (A3), U63.5 (A3)
i_reg_b5: J77.3, U61.4 (A4), U62.4 (A4), U63.4 (A4)
i_reg_b6: J77.4, U61.3 (A5), U62.3 (A5), U63.3 (A5)
i_reg_b7: J77.5, U61.2 (A6), U62.2 (A6), U63.2 (A6)

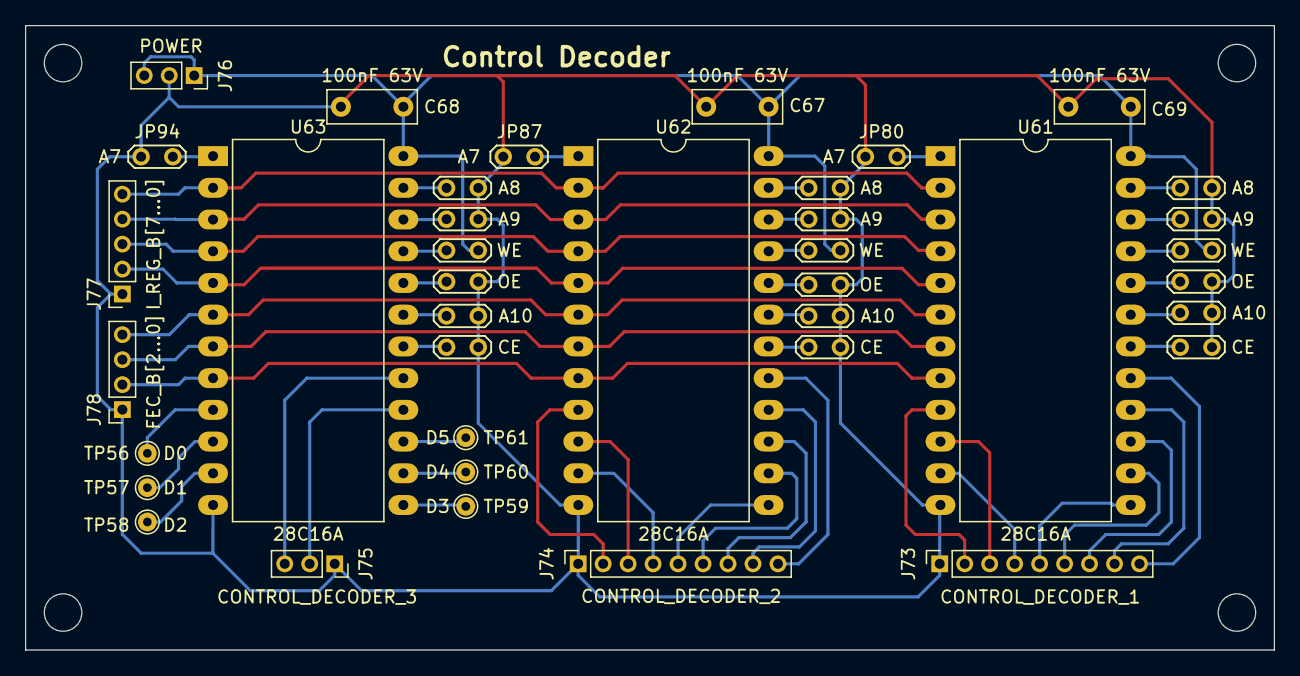
[picture p94: board Control Decoder.kicad_pcb from above]

Board: 2 copper layers, 100.0 x 50.0 mm, 39 parts (0 on the bottom side), 54 nets.
