rick0x00/8bit-computer/HARDWARE/EDA/KiCad/8-bit computer/B Register.kicad_pcb

## KiCad design HARDWARE/EDA/KiCad/8-bit computer/B Register.kicad_pcb (2021-08-03)

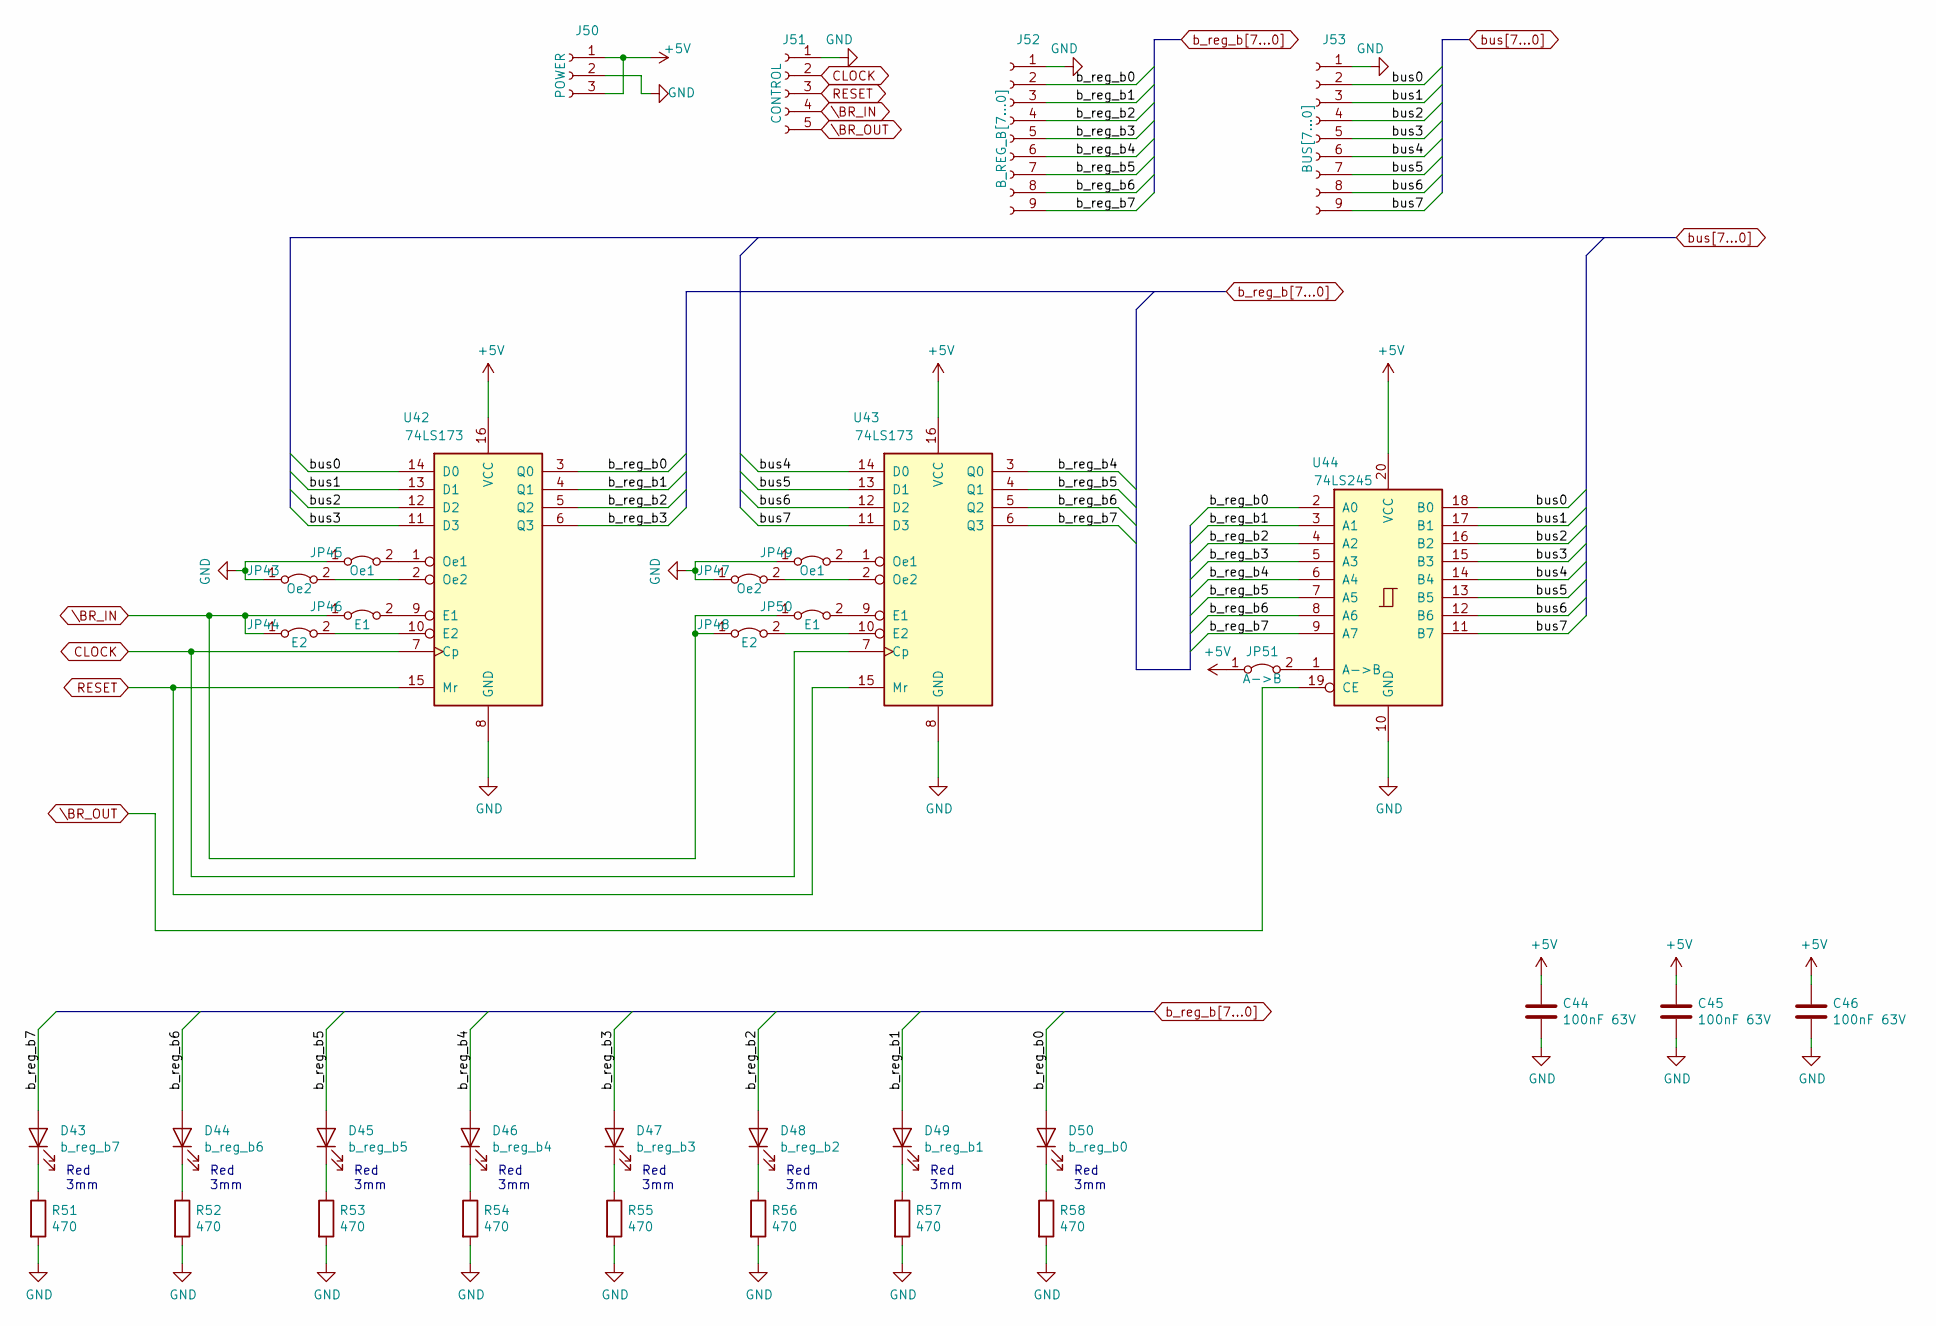
[picture p95: schematic B Register.sch]

Parts:
C44, C45, C46: 100nF 63V; C_Rect_L7.0mm_W2.5mm_P5.00mm
D43: b_reg_b7; LED_D3.0mm
D44: b_reg_b6; LED_D3.0mm
D45: b_reg_b5; LED_D3.0mm
D46: b_reg_b4; LED_D3.0mm
D47: b_reg_b3; LED_D3.0mm
D48: b_reg_b2; LED_D3.0mm
D49: b_reg_b1; LED_D3.0mm
D50: b_reg_b0; LED_D3.0mm
J50: POWER; PinSocket_1x03_P2.00mm_Vertical
J51: CONTROL; PinSocket_1x05_P2.00mm_Vertical
J52: B_REG_B[7...0]; PinSocket_1x09_P2.00mm_Vertical
J53: BUS[7...0]; PinSocket_1x09_P2.00mm_Vertical
JP43, JP47: Oe2; TestPoint_2Pads_Pitch2.54mm_Drill0.8mm
JP44, JP48: E2; TestPoint_2Pads_Pitch2.54mm_Drill0.8mm
JP45, JP49: Oe1; TestPoint_2Pads_Pitch2.54mm_Drill0.8mm
JP46, JP50: E1; TestPoint_2Pads_Pitch2.54mm_Drill0.8mm
JP51: A->B; TestPoint_2Pads_Pitch2.54mm_Drill0.8mm
R51, R52, R53, R54, R55, R56, R57, R58: 470; R_Axial_DIN0207_L6.3mm_D2.5mm_P7.62mm_Horizontal
U42, U43: 74LS173; DIP-16_W7.62mm_LongPads
U44: 74LS245; DIP-20_W7.62mm_LongPads

Connections:
+5V: C44.1, C45.1, C46.1, J50.1, J50.3, JP51.1 (A), U42.16 (VCC), U43.16 (VCC), U44.20 (VCC)
CLOCK: J51.2, U42.7 (Cp), U43.7 (Cp)
GND: C44.2, C45.2, C46.2, J50.2, J51.1, J52.1, J53.1, JP43.1 (A), JP45.1 (A), JP47.1 (A), JP49.1 (A), R51.2, R52.2, R53.2, R54.2, R55.2, R56.2, R57.2, R58.2, U42.8 (GND), U43.8 (GND), U44.10 (GND)
unnamed: D43.1 (K), R51.1
unnamed: D44.1 (K), R52.1
unnamed: D45.1 (K), R53.1
unnamed: D46.1 (K), R54.1
unnamed: D47.1 (K), R55.1
unnamed: D48.1 (K), R56.1
unnamed: D49.1 (K), R57.1
unnamed: D50.1 (K), R58.1
unnamed: JP43.2 (B), U42.2 (Oe2)
unnamed: JP44.2 (B), U42.10 (E2)
unnamed: JP45.2 (B), U42.1 (Oe1)
unnamed: JP46.2 (B), U42.9 (E1)
unnamed: JP47.2 (B), U43.2 (Oe2)
unnamed: JP48.2 (B), U43.10 (E2)
unnamed: JP49.2 (B), U43.1 (Oe1)
unnamed: JP50.2 (B), U43.9 (E1)
unnamed: JP51.2 (B), U44.1 (A->B)
RESET: J51.3, U42.15 (Mr), U43.15 (Mr)
\BR_IN: J51.4, JP44.1 (A), JP46.1 (A), JP48.1 (A), JP50.1 (A)
\BR_OUT: J51.5, U44.19 (CE)
b_reg_b0: D50.2 (A), J52.2, U42.3 (Q0), U44.2 (A0)
b_reg_b1: D49.2 (A), J52.3, U42.4 (Q1), U44.3 (A1)
b_reg_b2: D48.2 (A), J52.4, U42.5 (Q2), U44.4 (A2)
b_reg_b3: D47.2 (A), J52.5, U42.6 (Q3), U44.5 (A3)
b_reg_b4: D46.2 (A), J52.6, U43.3 (Q0), U44.6 (A4)
b_reg_b5: D45.2 (A), J52.7, U43.4 (Q1), U44.7 (A5)
b_reg_b6: D44.2 (A), J52.8, U43.5 (Q2), U44.8 (A6)
b_reg_b7: D43.2 (A), J52.9, U43.6 (Q3), U44.9 (A7)
bus0: J53.2, U42.14 (D0), U44.18 (B0)
bus1: J53.3, U42.13 (D1), U44.17 (B1)
bus2: J53.4, U42.12 (D2), U44.16 (B2)
bus3: J53.5, U42.11 (D3), U44.15 (B3)
bus4: J53.6, U43.14 (D0), U44.14 (B4)
bus5: J53.7, U43.13 (D1), U44.13 (B5)
bus6: J53.8, U43.12 (D2), U44.12 (B6)
bus7: J53.9, U43.11 (D3), U44.11 (B7)

Notes on the sheet:
Red 3mm

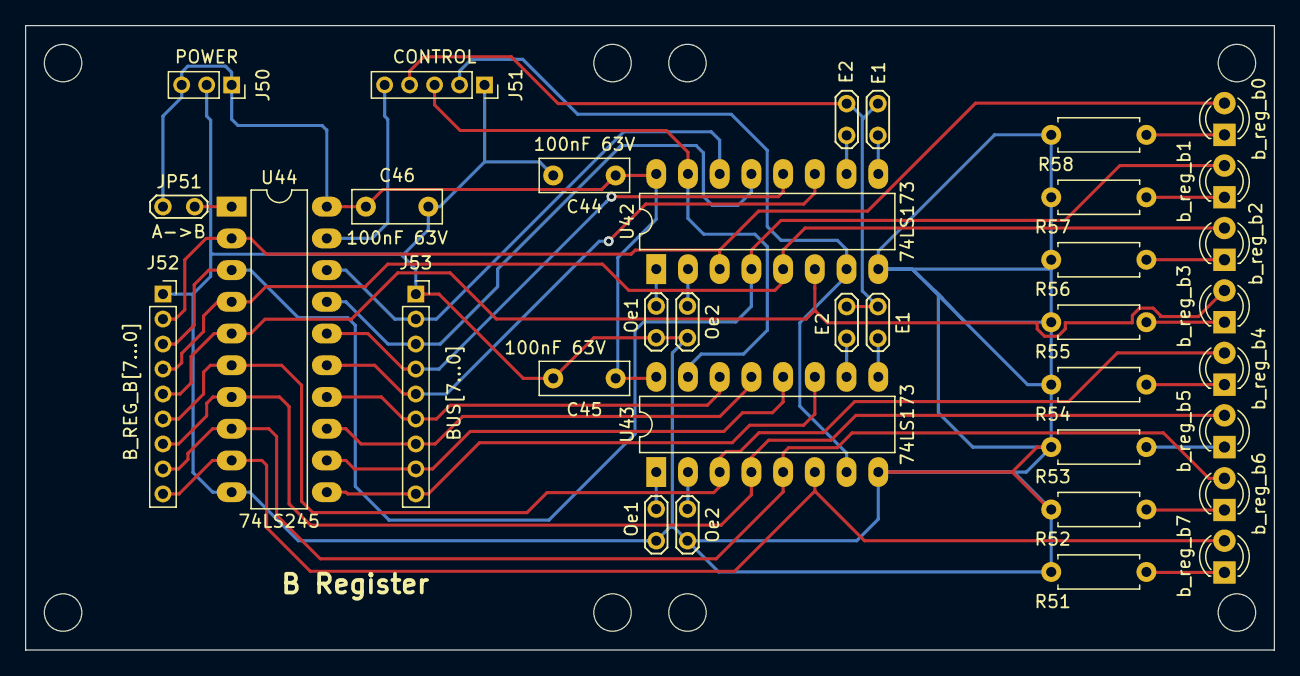
[picture p96: board B Register.kicad_pcb from above]

Board: 2 copper layers, 100.0 x 50.0 mm, 35 parts (0 on the bottom side), 39 nets.
