rick0x00/8bit-computer/HARDWARE/EDA/KiCad/8-bit computer/BUS.kicad_pcb

## KiCad design HARDWARE/EDA/KiCad/8-bit computer/BUS.kicad_pcb (2021-08-03)

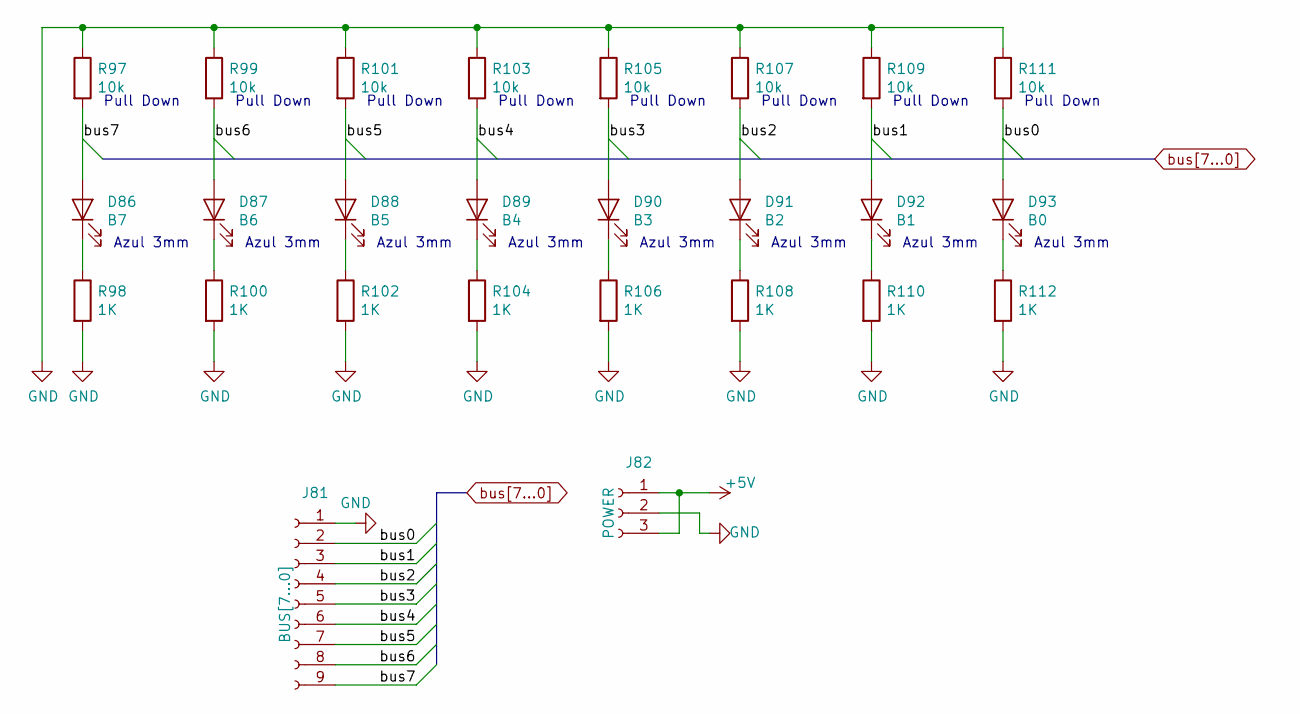
[picture p97: schematic BUS.sch]

Parts:
D86: B7; LED_D3.0mm_Clear
D87: B6; LED_D3.0mm_Clear
D88: B5; LED_D3.0mm_Clear
D89: B4; LED_D3.0mm_Clear
D90: B3; LED_D3.0mm_Clear
D91: B2; LED_D3.0mm_Clear
D92: B1; LED_D3.0mm_Clear
D93: B0; LED_D3.0mm_Clear
J81: BUS[7...0]; PinSocket_1x09_P2.00mm_Vertical
J82: POWER; PinSocket_1x03_P2.00mm_Vertical
R97, R99, R101, R103, R105, R107, R109, R111: 10k; R_Axial_DIN0207_L6.3mm_D2.5mm_P7.62mm_Horizontal
R98, R100, R102, R104, R106, R108, R110, R112: 1K; R_Axial_DIN0207_L6.3mm_D2.5mm_P7.62mm_Horizontal

Connections:
+5V: J82.1, J82.3
GND: J81.1, J82.2, R97.1, R98.2, R99.1, R100.2, R101.1, R102.2, R103.1, R104.2, R105.1, R106.2, R107.1, R108.2, R109.1, R110.2, R111.1, R112.2
unnamed: D86.1 (K), R98.1
unnamed: D87.1 (K), R100.1
unnamed: D88.1 (K), R102.1
unnamed: D89.1 (K), R104.1
unnamed: D90.1 (K), R106.1
unnamed: D91.1 (K), R108.1
unnamed: D92.1 (K), R110.1
unnamed: D93.1 (K), R112.1
bus0: D93.2 (A), J81.2, R111.2
bus1: D92.2 (A), J81.3, R109.2
bus2: D91.2 (A), J81.4, R107.2
bus3: D90.2 (A), J81.5, R105.2
bus4: D89.2 (A), J81.6, R103.2
bus5: D88.2 (A), J81.7, R101.2
bus6: D87.2 (A), J81.8, R99.2
bus7: D86.2 (A), J81.9, R97.2

Notes on the sheet:
Azul 3mm
Pull Down

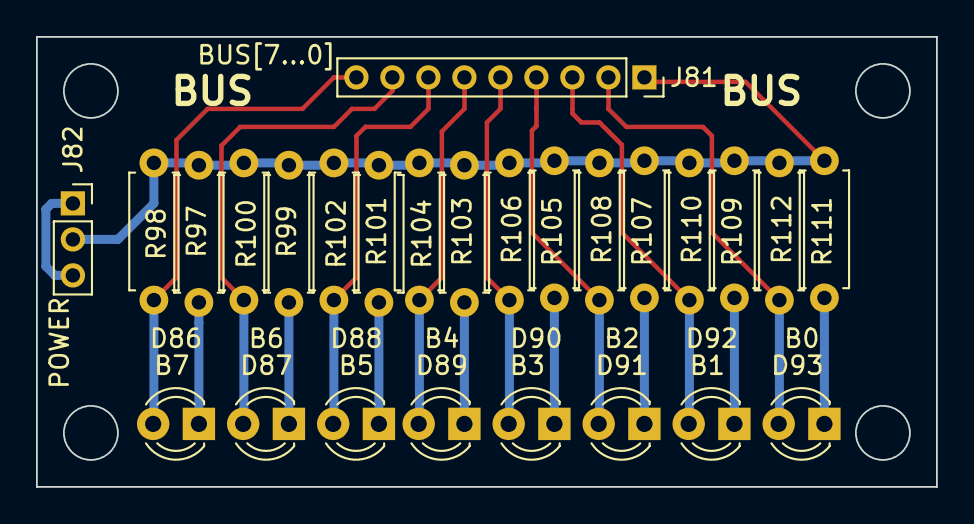
[picture p98: board BUS.kicad_pcb from above]

Board: 2 copper layers, 50.0 x 25.0 mm, 26 parts (0 on the bottom side), 18 nets.
